thereprocase/spool-wall-rack/designs/rev-g2/ef-triangulated-v1/README.md

# E + F direct-brace body

Implemented CAD: a six-millimetre-wide diagonal connects the lower mounting region directly to the keel. The upper mast retains the six-millimetre web and tapered shoulders from ef-cut-v4. Protected G bearing/capture geometry has zero symmetric difference; fixed mounting and moulding checks pass.

The original two-wall, 0.6 mm skin schedule in selected-layout.json was not sliced. Subsequent implemented ASA schedules retain this body and use 1.6 mm skins. They provide aligned body/helper STEP files, model-only 3MF, actual slices and verification.

https://github.com/thereprocase/spool-wall-rack/tree/main/designs/rev-g2/print-controls

CAD validity does not establish structural performance or physical print qualification. Sacrificial bridges receive zero structural or bond credit.

Combined STEP

https://raw.githubusercontent.com/thereprocase/spool-wall-rack/main/designs/rev-g2/ef-triangulated-v1/bracket-with-modifiers.step

Body and individual aligned helper STEPs

https://github.com/thereprocase/spool-wall-rack/tree/main/designs/rev-g2/ef-triangulated-v1
