thereprocase/spool-wall-rack/designs/rev-g2/evolution/f9ad9cdbc331/README.md

# G helper candidate f9ad9cdbc331

Selection role: **balanced**. Experimental CAD, not a qualified bracket or load rating.

[Combined body/helper STEP](bracket-with-modifiers.step) · [Model-only 3MF](rev-g-model-and-modifiers.3mf) · [Body STEP](body-only.step) · [Actual Orca slice and settings](slice-evidence.zip)

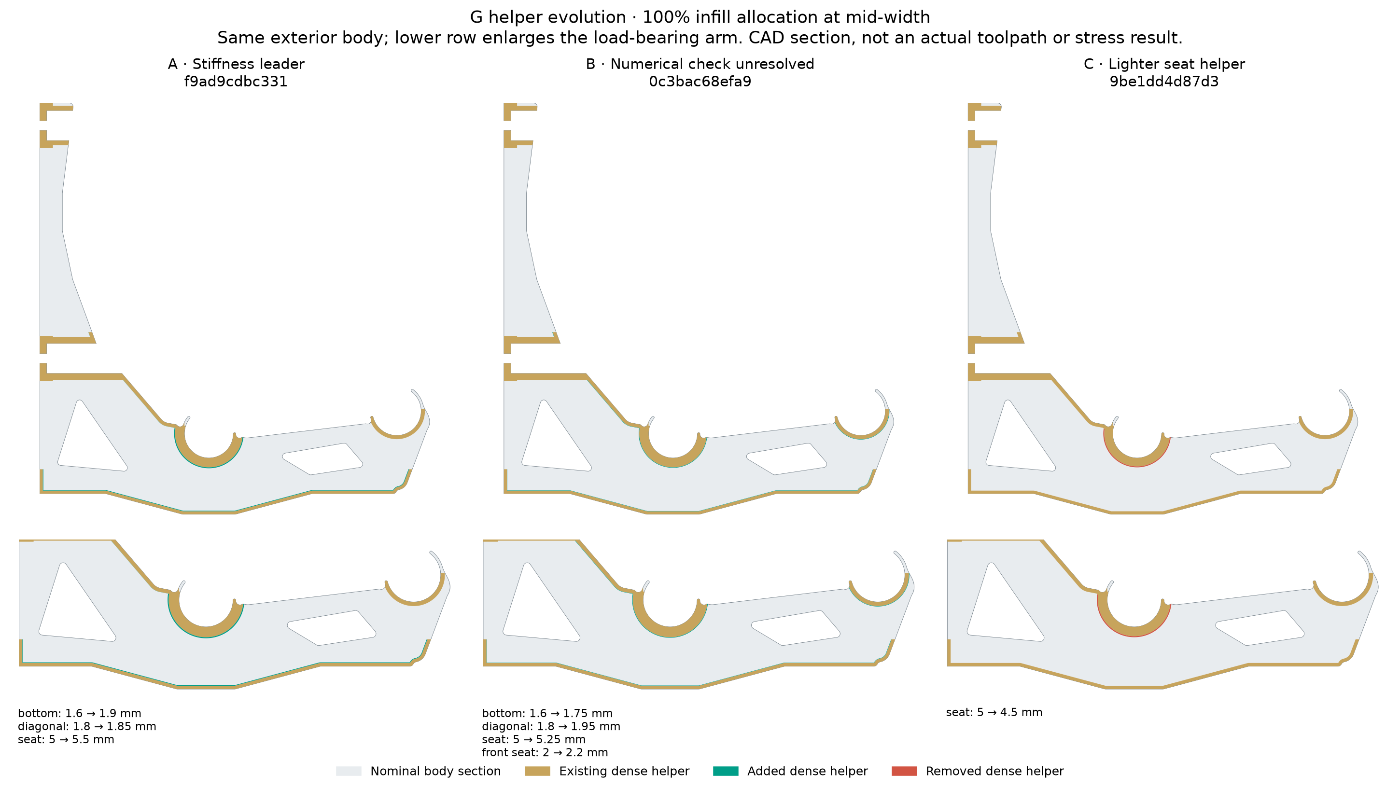
[picture p52: analysis/rev-g2/evolution-results/batch-02/helper-directions.png]
Helper allocation comparison


The exterior body is byte-identical to G. These dimensions change the aligned 100% infill helper allocation:

| Parameter | mm |
|---|---:|
| bottom band | 1.9 |
| diagonal band | 1.85 |
| seat band | 5.5 |
| front seat band | 2 |
| lower tunnel collar mm | 3.5 |
| upper tunnel collar mm | 2.5 |

Import the model-only 3MF as one object with multiple parts. The body prints; the three helpers are 100% rectilinear infill modifiers. External tabs and halos must stay modifiers. Use OrcaSlicer, P1S/0.4 mm, calibrated PETG settings, at least two walls, five 0.2 mm top/bottom layers and 0% base infill. STEP carries geometry and alignment, not slicer roles.

Individual helpers: [dense chords and seats](dense-chords-and-seats.step), [lower internal plane](rib-plane-lower.step), [upper internal plane](rib-plane-upper.step). [CAD checks](helper-verification.json), [body provenance](source-verification.json), [3MF role checks](3mf-verification.json), [hashes](SHA256SUMS.json).

At 12 kg, the retained-material screen gives **4.1295 mm** maximum movement and **20.4292 MPa** raw tensile stress. Contact and equilibrium pass at the stated 1e-5 screen tolerance. The model omits 8.12% of nominal raw plastic.

The completed full-cell refinement on the same retained material gives
**4.1547 mm** maximum movement and **19.6792 MPa** raw tensile peak. The maximum
change across all 10,234,400 compared nodes is 0.025293 mm. All 67,740,528
stress samples are retained. Active preparation, solve, audit and comparison
take 5 min 18 s. This checks adaptive coarsening error; boundary omission and
physical qualification remain unresolved. Small raw-stress differences are
not a demonstrated strength ranking.

[Full-cell audit](../../../../analysis/rev-g2/evolution-results/batch-02/leader-refinement/audit.json) ·
[Mesh comparison](../../../../analysis/rev-g2/evolution-results/batch-02/leader-refinement/mesh-comparison.json).

[Detailed 3D audit](../../../../analysis/rev-g2/evolution-results/batch-02/f9ad9cdbc331/audit/audit.json) · [Search workflow and qualification limits](../../../../analysis/rev-g2/EVOLUTION.md).

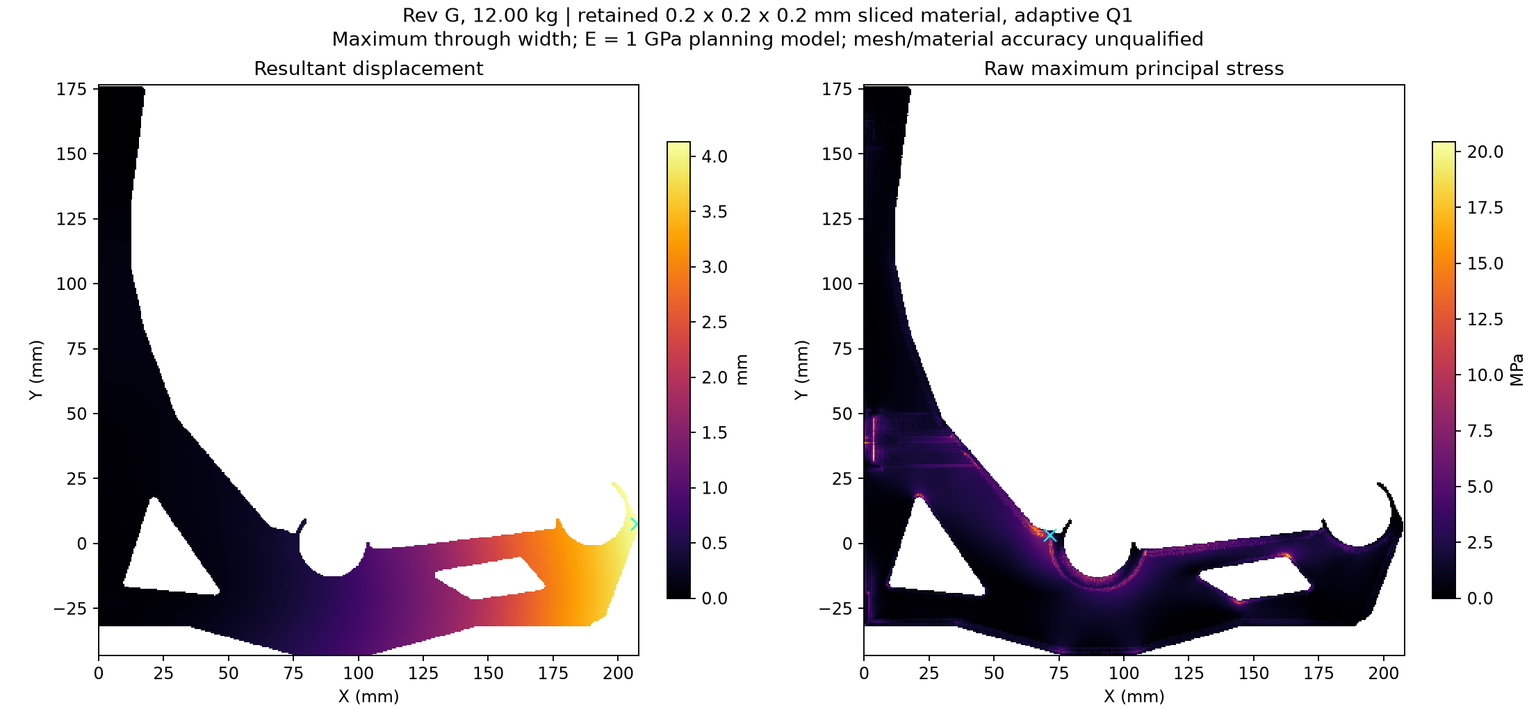
[picture p53: analysis/rev-g2/evolution-results/batch-02/f9ad9cdbc331/audit/g-results.png]
Retained-material movement and raw stress
