thereprocase/spool-wall-rack/designs/rev-g/studies/seed1-best/README.md

# Rev G seed-1 coarse best — rejected diagnostic candidate

Candidate `82e88fcf29749880c5c3` uses thin shaped planes. It slices to
**84.35 g**, but gives 4.930 mm vertical movement, 5.034 mm mean seat
translation magnitude and 120.46 MPa raw maximum tensile stress in the h2
3D model. Its fine 2D movement of 4.001 mm already narrowly exceeds the
4 mm bracket planning screen. No acceptance is claimed.

The 3MF imports all three modifiers in alignment and keeps windows/tabs empty,
but minimum dense footprint coverage is only 94.98% at an upper-skin bridge
transition. The failed coverage gate remains recorded.

[Exact parameters](selected-layout.json) · [Actual toolpath audit](toolpath-verification.json)
· [Model-only 3MF](rev-g-model-and-modifiers.3mf)
· [Raw mechanics](../../../../analysis/rev-g/studies/seed1-best/README.md)
· [Study report](../../../../analysis/rev-g/README.md).
