thereprocase/spool-wall-rack/analysis/rev-g/studies/full-plane-best/README.md

# Full-plane feedback finalist — three-mesh evidence

The actual slice is 103.76 g. All three saved meshes pass independent
equilibrium/contact gates but fail the raw 10.125 MPa tensile screen.
The fine peak is 55.05 MPa; it is not a converged rupture allowable.

| Mesh | Complete finite field | Equilibrium results | Mesh audit |
|---|---|---|---|
| h2 | [NPZ](print-material-1w-h2-solution.npz) | [JSON](print-material-1w-h2-results.json) | [JSON](print-material-1w-h2-mesh-quality.json) |
| h1.5 | [NPZ](print-material-1w-h1.5-solution.npz) | [JSON](print-material-1w-h1.5-results.json) | [JSON](print-material-1w-h1.5-mesh-quality.json) |
| h1 | [NPZ](print-material-1w-h1-solution.npz) | [JSON](print-material-1w-h1-results.json) | [JSON](print-material-1w-h1-mesh-quality.json) |

[Geometry audit](geometry-1w.json) · [Parameters](selected-layout.json)
· [Search provenance](search-selection.json) · [Quadratic buckling](../../BUCKLING.md)
· [Actual CAD/slicing](../../../../designs/rev-g/studies/full-plane-best/README.md)
· [Raw-peak metrics and interpretation](../../README.md).
