thereprocase/spool-wall-rack/analysis/rev-g/studies/seat-support/README.md

# Wider inner-seat support — rejected 3D feedback perturbation

The 5 → 8 mm inner-seat support change reduces coarse front movement to
2.988 mm, but the raw h2 tensile peak is 21.25 MPa. The actual slice is
108.03 g. No refined strength acceptance is claimed.

[Design rationale](design-rationale.json) · [Parameters](selected-layout.json)
· [Complete h2 field](print-material-1w-h2-solution.npz)
· [Equilibrium results](print-material-1w-h2-results.json)
· [Mesh audit](print-material-1w-h2-mesh-quality.json) · [Geometry audit](geometry-1w.json)
· [Actual CAD/slicing](../../../../designs/rev-g/studies/seat-support/README.md)
· [Full study](../../README.md).
