thereprocase/spool-wall-rack/analysis/rev-g/studies/seed1-best/README.md

# Thin seed-1 candidate — retained failure evidence

The complete h2 field gives 4.930 mm vertical movement and 120.46 MPa raw
maximum tensile principal stress. Movement, strength and actual dense-path
coverage fail. No finite stress cells are removed.

[Raw solution](print-material-1w-h2-solution.npz) · [Equilibrium results](print-material-1w-h2-results.json)
· [Mesh audit](print-material-1w-h2-mesh-quality.json) · [Geometry audit](geometry-1w.json)
· [Parameters](selected-layout.json) · [Search selection](search-selection.json)
· [Actual CAD/slicing](../../../../designs/rev-g/studies/seed1-best/README.md)
· [Full study](../../README.md).
