thereprocase/spool-wall-rack/RESTART-2026-09-11.md

# Current restart: recovered E13 ASA reference and rejected EF core trial

Read designs/rev-g2/print-controls/README.md and RECOVERED-PRINTS.md first. A read-only recovery found the completed overnight ASA slice associated with E13: seven walls, 10% base infill, 1.6 mm minimum skins and two objects. Its associated downloaded STEP is byte-identical to the published E13 assembly. The newer STEP is G. The saved G PETG project uses two walls and 10% base infill with all three helpers, but was saved after print start. The exact original PETG submission was overwritten; current archive/cache use a later PLA profile. Do not call the deliberate eight-wall G control a recovered successful physical print.

Current EF direct-brace body and continuous core are built and sliced, with aligned helper STEPs, complete source hashes and raw bond audits. Four walls / 1.6 mm skins in ASA use 91.970652 cm3, versus deliberate G eight-wall control 118.660028 cm3. Gross cut 27.048%, core reinvestment 5.406 cm3, net saving 22.492%. Local credited routes pass, but the part fails the movement allocation.

Intermediate 1e-4 contact diagnostics: thick G 2.672976 mm, raw tensile peak 21.000368 MPa; EF core 4.981787 mm, raw peak 32.195513 MPa. Omitted raw nominal material is 4.734% and 8.902% respectively. Both tighter 1e-5 attempts fail their time bounds. Preserve every field and raw failure. Do not label either a tight accepted result or a physical rating. Core refinement and a winning broad architecture remain unfinished.

Raw controls are under analysis/rev-g2/.work/print-controls. G's accepted intermediate is g-asa-8w-1p6/finish-02/discovery; core is ef-core-asa-4w-1p6/finish-01/discovery. Each has failed tighter solve evidence and a separate intermediate audit. Original printer recovery data, identifying job records and source archives remain only in ignored analysis/rev-g2/.work/print-recovery. Do not publish those raw archives. The public receipt is designs/rev-g2/print-controls/recovered-print-evidence.json.

Next: use the recovered successful E13 schedule as the physical-reference lead, preserving its geometry association limits; use deliberate G controls to isolate architecture and wall count. Restore or capture the actual submitted PETG slice before calling it matched. Reassess direct frame bending and the forearm using the current fields; do not keep adding core material after the stiffness failure. The broad fast-ranking method and material-converged qualification remain unfinished. Existing GPU fixtures, previous G pilot, failed EF diagnostics and all old CPU caches stay preserved. No stopped whole-part CPU meshing was restarted.

## Prior checkpoint history

# Restart handoff: implemented EF cut and localized reinforcement

**Latest implemented work:** `analysis/rev-g2/EF-RESULTS.md`. The selected E+F
body is now built and sliced. Protected G seat geometry has zero CAD XOR;
mounting axes and 25.4 mm horizontal moulding underside pass their checks.
Five implemented schedules have complete aligned STEP/helper handoffs.

`ef-cut-v3` cuts 29.211% of matched G spent extrusion. `ef-reinvest-v1` adds
6.342 cm3 at inner-seat/forearm, wall/upper-brace and seat/keel-post transitions,
leaving 20.653% net saving. Mechanics are underway; do not promote either as a
load-qualified winner. If local reinforcement needs more budget, cut from
low-stress/low-strain-energy regions while rechecking all load cases,
connectivity, stability and print support. Track gross cut, added back and net
saving separately. No need to ask again about the moulding datum.

The heavier first EF reference has an accepted 1e-5 contact screen:
5.660824 mm movement and 39.997226 MPa raw tensile peak, worse than G. The
successful solve first settles contact at 1e-4, then verifies it at 1e-5.
The final check takes 59.75 s including all stress export, after 271.81 s
contact discovery. Earlier strict-from-start and stronger-coarse failures
are retained. This timing excludes initial failures and geometry/CAD setup.
Current cut/reinforced pipeline attempts live under each candidate's
`analysis/rev-g2/.work/<candidate>/check-01`. Public receipts are under
`analysis/rev-g2/ef-hybrid-results/`. No old CPU whole-part meshing was restarted.

**Earlier continuation context:** [six broader body sketches](designs/rev-g2/shape-seeds/README.md)
and [fixed interface contract](designs/rev-g2/INTERFACE-CONTRACT.md). The body
must no longer be copied unchanged from G. Change outer contours, depth, braces,
windows and through-width material arrangement. Keep rods at `(90,0)` and
`(190,12)` in XY and mounting axes at `(164,12)` and `(40,12)` in YZ, plus spool
clearance. The locating datum is now resolved: printed G brackets slide down
the wall until their bottom edge rests on the crown moulding. Preserve the
lower wall corner at X=0, Y=-32 mm and the rod/mount heights relative to it.
Keep the underside horizontal for at least 25.4 mm outward from the wall
before descending. Actual moulding projects 19.05 mm. This replaces the
15 mm estimate; do not use the old 215 mm limit or local E13-minus-8-mm floor.
The selected next body is E plus F: deeper E frame with F-derived seat backing.
The six new seeds are connected XY sketches with a spool-clearance check,
not CAD/STEP handoffs or a mechanically ranked family set.

The local G pilot is completed and preserved. Two of its three actual-slice
finalists converge; the other fails both its initial solve and bounded retry.
The leader's same-material uniform 0.2 mm refinement completes in 318.10 active
seconds, giving 4.154745 mm maximum movement, 19.679217 MPa raw tensile peak,
and 0.025293 mm maximum change across all 10,234,400 compared nodes. All
67,740,528 stress samples survive. See the loop's calibration and leader-refinement
receipts. It still exceeds the 4 mm allocation, retains 8.12% material omission,
and does not establish strength or transfer accuracy for new architectures.

**Completed local method pilot:** [staged evolutionary screening](analysis/rev-g2/EVOLUTION.md).
The local G helper screen now evaluates 100 new proposals in 11 min 18 s.
The first real CAD/slice/3D finalist pass took 6 min 55 s. Use the loop page
and its receipts for finalist and refinement status. This screening workflow
supersedes the earlier requirement to finish all material qualification before
running local allocation experiments. Qualification gates remain intact.

New scripts are `evo_screen.py`, `evo_search.py`, `evo_verify.py`,
`evo_refine.py`, `evo_transfer.py`, `evo_uniform.py` and `evo_report.py` under
`analysis/rev-g2`. `evo_refine.py --prepare-only` permits CAD/material preparation
while another candidate uses the GPU; `--resume` runs its solve and audit.
Reported active-stage time excludes time parked between those invocations.
Keep GPU solves sequential on the 12 GiB device.

The actual P1S material parser now restores the configured nozzle offset.
Preserve the superseded P1S caches. Historical G mechanics uses a zero-offset
slice and is unchanged. Fresh corrected P1S evidence and all candidate fields
live under `analysis/rev-g2/.work/evolution`; no raw evidence is deleted.

Fresh 10.75 / 12 / 13.25 kg G contact checks are documented in [G results](analysis/rev-g2/G-RESULTS.md). One spool changes bracket movement by about 0.452 mm; material accuracy and physical qualification remain open.

This is the current restart checkpoint. The long whole-part CPU meshing route
has been stopped. Preserve the current working tree, including untracked raw
attempts and ignored runtime caches. Do not restart the old fTetWild jobs.

**Current continuation:** [G results, numerical sensitivity and limits](analysis/rev-g2/G-RESULTS.md).
The retained 0.2 mm material now has a completed unilateral wall-contact screen:
4.335477 mm maximum movement and 20.025374 MPa raw peak tensile stress at 12 kg.
A 1e-6 relative solve check keeps the 6,426-node contact footprint and changes
all nodal displacements by at most 4.894e-7 mm versus the 1e-5 screen.
This does not pass the original stricter solver gate or establish material
accuracy: 8.0177% of raw nominal material is omitted. See the result page for
fresh spool-load checks, preserved failures and final checkpoint receipts.

**Resume from the completed contact state**, not from the original bilateral
wall restraint. The coarse correction and changed-load contact fixtures pass.
The next principal uncertainty is finer material/mesh convergence on G and
transfer to the fresh P1S/PETG slice. Keep all raw stress fields, earlier failed
iterates and geometry caches. No old CPU meshing job should be restarted.

**Previous continuation:** [adaptive mesh and full-G trial evidence](analysis/rev-g2/ADAPTIVE-MESH.md).
Two-level constrained hex coarsening and its CUDA operator pass independent
mechanical fixtures. Protecting G's interfaces and split-bond neighborhoods
reduces 8,265,873 fine cells to 4,096,575 leaves. Both full-G GPU trials failed
linear convergence; all fields and peaks survive. A separate geometry census
reaches 0.025 mm XY boundary cells with 1.10% omitted raw material, before
grading/constraints/mechanical refinement. A fresh P1S/PETG slice and raw shape
were built after accounting separately for startup priming extrusion. They
have not replaced the historical shape in a converged mechanics loop.

**Previous continuation:** [GPU validation and reproduction](analysis/rev-g2/GPU-VALIDATION.md).
Warp 1.17.0 is installed and tested on the RTX 3080 Ti. The upstream elasticity
comparison, independent 3D hollow-material/contact fixtures and manufactured
patch tests on G's actual raw slice crop pass. Conservative voxel geometry
still removes 4.31% of that crop at 0.1 mm XY / 0.2 mm Z spacing. This is not
an accepted whole-G material mapping, load solution or strength result.

## Current candidates and decisions

[STEP/helper download index](PRINT-CANDIDATES.md) lists all implemented recent ideas and the five current G recheck schedules. Every future idea checkpoint must include aligned body/helper STEP files and notes. G2 concept-family CAD and helper exports are required unfinished work after restart.

- [Rev G research finalist and CAD](designs/rev-g/README.md): latest implemented
  research geometry. It is not a qualified design. Its original structural
  approximation is superseded for interpreting actual printed material.
- [E13 handoff](designs/closed-wall-e13/README.md): preserved earlier prototype evidence;
  it does not acquire new qualification from G2 work.
- [G2 architecture worksheet](designs/rev-g2/ARCHITECTURE-WORKSHEET.md): seven
  preparatory families, not seven completed CAD candidates. No G2 architecture
  has been built, ranked, or accepted.
- [G2 requirements](G2-BRIEF.md) and the current interface contract govern the
  new study. Existing outlines and helper count/shape are soft; reference rod
  and mounting positions now stay fixed. The matching moulding locating datum
  and one-inch horizontal reach replace assumed old silhouette constraints.
- [GPU execution checkpoint](analysis/rev-g2/GPU-VALIDATION.md) follows the
  [software review](analysis/rev-g2/GPU-FEM-REVIEW.md). Warp's Apache-2.0 license,
  tagged example hash and wheel/JIT CUDA execution are verified. DTU reuse
  permission was not established and its code was not incorporated. The tested
  GPU backend is a starting point; its current full-cell material approximation
  and diagonal preconditioner are not qualified for a whole-G solve.

## Preserved requirements

P1S, 0.4 mm nozzle, PETG or ASA, at least two walls, 0% base infill and 100%
helper regions. Sacrificial 0.4 mm bridge extrusion counts toward spent plastic
but receives zero stiffness, strength or bonded-connection credit. Keep all
finite stress cells and raw peaks. No percentile substitution.

Reference load is 12 kg / 117.72 N per bracket. Total loaded movement limit is
5 mm; the provisional rail/mount reserve is 1 mm, leaving 4 mm for bracket
resultant movement. Adding/removing a 1.25 kg spool requires a new contact solve
and at most 1 mm total movement change. The effective 1 GPa modulus is a
planning assumption, not measured lifetime behavior. Sustained 85 F and brief
loaded 100 F exposure, nominal fracture factor four, rail sag, mount slip,
creep, fit and print-process qualification remain explicit gates.

## Completed sliced-material work

[Analysis overview and reproduction](analysis/rev-g2/README.md) links the raw
slice archives, independent validation, process audit and reference shape cache.
Five schedules were actually sliced: 2w/2 skins, 2w/5 skins, 2w/8 skins,
8w/2 skins and 8w/8 skins; each skin layer is 0.2 mm. G's body and three original
helpers were copied without geometry changes. All five effective process
settings and P1S bed/exclusion checks passed.

The independent 50,000-sample shape check passed outside the stated 0.005 mm
polygonization uncertainty. It uses analytical distances to variable-width
paths rather than querying the same polygon union twice. Thick bridges are
excluded before connectivity and geometry queries.

| Schedule | Credited E volume, mm3 | Sacrificial E volume, mm3 | Nominal structural union, mm3 |
|---|---:|---:|---:|
| 2w / 2 skins | 60373.785 | 6901.280 | 61393.747 |
| 2w / 5 skins | 70979.802 | 6940.469 | 71890.970 |
| 2w / 8 skins | 81247.882 | 6928.297 | 82057.762 |
| 8w / 2 skins | 103417.432 | 5060.135 | 104686.248 |
| 8w / 8 skins | 119735.998 | 5089.798 | 120769.740 |

Nominal footprint volume is a separate continuum quantity from extrusion E.
Do not erase the difference or call them equal. The reference cache loads in
about 1.6 s; 10,000 occupancy queries took about 0.06 s on this machine.

`PlasticShape.integrated_volume(regions)` integrates exact polygon intersections
through all layers. Independent analytic slab fixtures pass for raw/continuum,
empty, disjoint and overlapping queries, with one/four workers. The whole
reference projection agrees with nominal volume within about 2.1e-8 mm3.

## Latest completed mechanical diagnostic

The final reduced reference uses exact material-volume integration per P1
triangle. All finite triangles are retained, and no stiffness is inserted at
empty quadrature samples. The two runs are:

| Mesh | Triangles | Front mean vertical movement, mm | Global maximum resultant, mm | Raw tensile peak, MPa |
|---|---:|---:|---:|---:|
| h2 | 37985 | 3.097760 | 3.462327 | 13.230930 |
| h1 | 70035 | 3.111314 | 3.477636 | 11.741875 |

Front movement changes about 0.44%. Both retain nonzero wall gaps and pass free
residual, force, moment, nonpenetration and active-reaction checks. The full
finite displacement, stress, material-volume, force and reaction fields are in
[reduced-plastic](analysis/rev-g2/reduced-plastic). Use only the filenames with
`-exact-h1` or `-exact-h2` for the current reference.

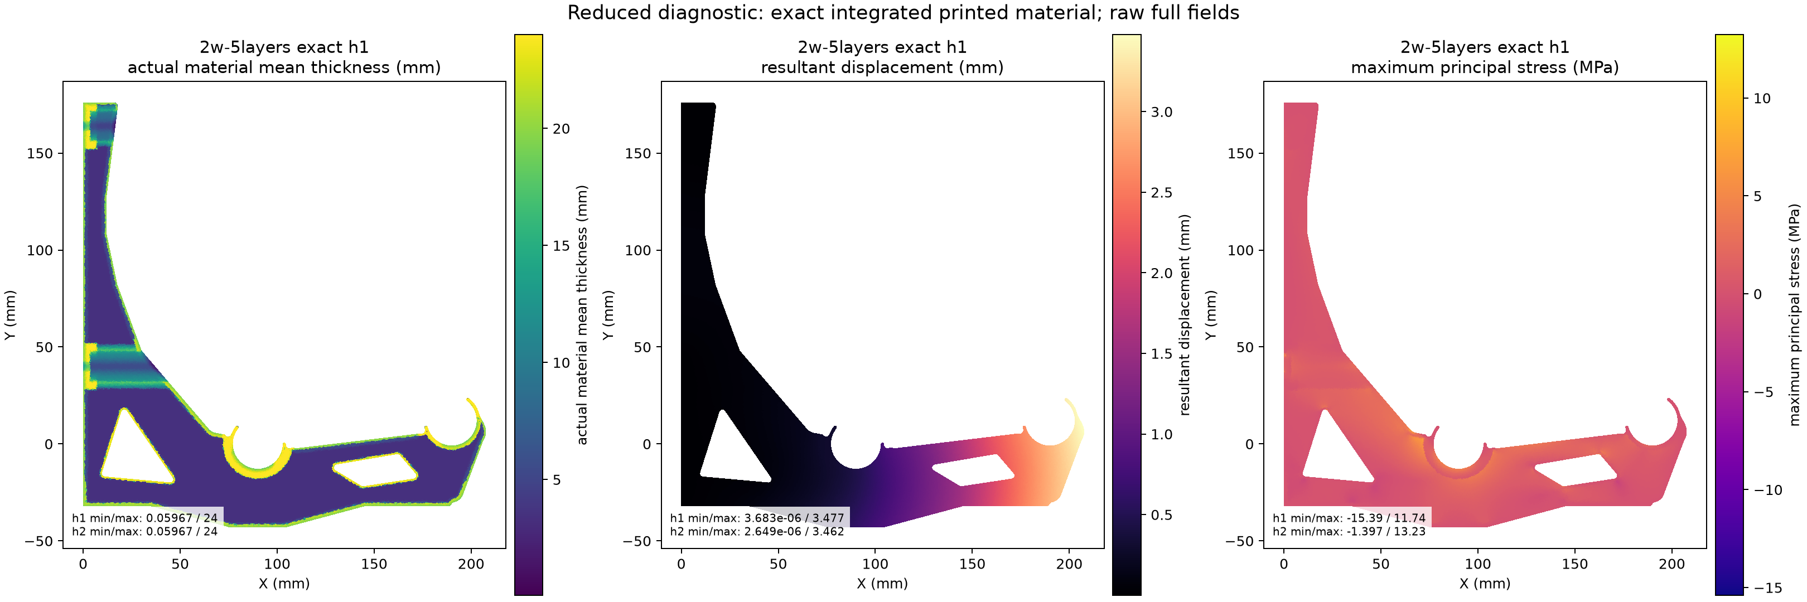
[picture p55: analysis/rev-g2/reduced-plastic/exact-recheck.png]
Latest reduced diagnostic


This is plane stress with displacement uniform through bracket width and
fixings projected to the wall boundary. It collapses the actual 3.6 mm washer
plane and through-width response. It is not a 3D strength result. Raw peak
stress is not converged. No corrected 4x fracture margin is established.

The attempted extension to the other schedules is unfinished: 2w/2 skins hit
the positive integrated-element-volume assertion, and 2w/8 skins exited during
integration without a result. Neither eight-wall reduced run was completed.
Investigate these failures before claiming a complete reduced matrix. Earlier
quadrature-based beta outputs remain local historical attempts and are not the
accepted diagnostic.

The actual production contact kernel passes analytic opening, closing,
touching and release fixtures. Affine elasticity/stress and rigid motions also
pass. [Fixture report](analysis/rev-g2/validation/mechanics-fixtures.json).

## 3D failures and why the route changed

[Meshing notes](analysis/rev-g2/MESHING-NOTES.md) retain the attempt history.
The reference continuum uses 0.03 mm closing, pore areas below 0.16 mm2,
0.02 mm XY simplification and a 0.01 mm coordinate grid. Its volume is
71949.034 mm3, with a 206.314 mm3 symmetric difference from raw footprints.
Raw nominal layers remain separately preserved.

TetGen recovered the boundary and 39 enclosed voids, but quality refinement
failed. Its boundary-only mesh has 662332 retained tetrahedra after auditing
268 numerically collapsed cells. The cleanup introduces 67 nonmanifold boundary
edges and artificial internal faces as far as 0.4 mm from the intended surface.
It is rejected despite nearly exact total volume. Netgen optimization crashed;
rounding and T-junction repair did not produce an accepted quality mesh.

Both fTetWild G jobs remained CPU-active for over an hour without returning a
mesh. They were explicitly terminated and process absence verified. No G 3D
solve was accepted. Small hollow-box meshing/refinement fixtures do not prove
the bracket is solved.

## Local evidence and tools to preserve

The active branch is `codex/rev-g2-architecture`; the public delivery branch is
`main`. This checkout was created independently of the earlier Rev G worktree.
Do not reset/clean either worktree, delete raw attempts, or modify E13/G records.

Current scripts and outputs are under `analysis/rev-g2` and `designs/rev-g2`.
The established native worker is `analysis/rev-g/run_native.py`; the Python
environment and installed Orca application are outside the repository. Base
dependencies are in `analysis/e13/requirements.txt`, with additional isolated
packages listed in `analysis/rev-g2/requirements-extra.txt`.

The new GPU runtime is separate from that native CAD environment. Its pinned
dependencies are in `analysis/rev-g2/requirements-gpu.txt`; instructions are in
the GPU checkpoint. `gpu_benchmark.py`, `gpu_hex.py`, `validate_gpu_hex.py` and
`gpu_material_probe.py` reproduce the new backend, numerical fixtures and slice
crop tests. Accepted and rejected numerical fields are in
`analysis/rev-g2/gpu-validation`, including its `failures` and `refinement`
directories. The latter contains the complete finer crop fields, not a G solve.

Keep these local runtime/evidence locations, even when they are not published:

- `analysis/rev-g2/.work/python`: isolated native meshing dependencies.
- `analysis/rev-g2/.work/integrated-thickness`: exact-integration caches.
- `analysis/rev-g2/.work/*gpu*research.md`: supplementary software research.
- `analysis/rev-g2/.work/gpu-route`: runtime discovery snapshots and raw GPU
  logs, including initial failed comparisons and the fixture count correction.
- `analysis/rev-g2/g-recheck/2w-5layers/fallback-investigation`: raw failed
  repair/refinement experiments and their reports. Some exploratory scripts
  still need review before redistribution or reuse.
- Other local continuum/decimation attempts, original uncompressed layer JSON,
  duplicate G CAD copies and untracked native debug STL files. They are not new
  accepted designs. The published slice ZIPs preserve the canonical raw inputs.

No analysis worker from the latest G jobs needs to survive the restart. Do not
terminate unrelated historical processes merely because their names are Python.

## Resume sequence

1. Read this handoff, `AGENTS.md`, `G2-BRIEF.md`, the analysis README and GPU
   review. Verify the current git state; preserve uncommitted work.
2. Continue from the tested Warp backend. Upstream default-tolerance stress
   comparisons failed; the explicitly tighter default-case comparison passes
   the original gate. Independent affine/rigid, hollow-wall, 3D bar contact,
   edge/corner bond and sacrificial-connector fixtures pass. Preserve all raw
   results; these checks do not establish whole-bracket mechanics.
3. Resolve the measured voxel boundary loss and full-part bond representation
   with a bounded adaptive/cut-cell or sufficiently converged full-cell study.
   The current crop loses 17.12%, 8.37% and 4.31% at successively finer XY grids.
   Check long thin bending and practical preconditioning before full-G scale;
   the earlier diagonal-only solver has now been supplemented by the tested
   auxiliary coarse correction in `gpu_multigrid.py`. Avoid returning to
   unbounded whole-part tetrahedral meshing.
   Continue from `gpu_demo_adaptive.py` and `gpu_demo_adaptive_operator.py`:
   two-level constraints now pass, and `gpu_demo_boundary.py` quantifies finer
   full-G material recovery. Extend grading/constraints to that boundary mesh
   using the completed contact state and the tested coarse correction. The
   existing diagonal-preconditioned full-G trials failed even after 12,000
   continuation iterations. Fresh P1S/PETG priming accounting is repaired;
   preserve its distinct raw shape and the original accounting failure.
4. Adapt and verify the actual seat loads, washer plane, bore restraints and
   nonzero-gap wall interfaces. Recheck G with corrected 3D material and mesh
   sensitivity, then the changed spool load. Repair the unfinished reduced
   matrix application as needed.
5. Only then build and compare the six-or-more G2 architecture families, obtain
   early 3D feedback, optimize survivors, and publish the complete candidate
   ledger. No preferred prototype until all computational gates pass.

Physical qualification and measured dowel dimensions remain outstanding. A
simulation result alone must never become a released spool rating.
