thereprocase/spool-wall-rack/docs/archive/AGENTS-2026-09-11.md

# Project instructions

Keep this repository current as the design progresses. Checkpoint completed geometry and its verification with clear commit messages. Keep the current prototype obvious in README; preserve superseded useful revisions separately.

Do not commit personal information, private conversation transcripts, credentials, local absolute workspace paths, or identifying account data in project content. Use a generic project identity for git commits.

Current path is the closed-wall, continuous-plate bracket. Keep the future open-web exploration separate. Preserve full L-shaped internal plates parallel to printer XY and installed bending plane. Do not replace them with transverse grids.

Print assumptions: 0.2 mm layers; 1.2 mm top and bottom; 15% infill gets zero structural credit. E6 uses 2.4 mm modeled structural perimeter, superseding the original three-perimeter assumption locally; verify actual sliced paths. Internal and exterior side plates remain 1.2 mm. Snap fingers are separately dimensioned.

Do not assign safe spool counts from generic tensile strengths. State limits of geometric checks and distinguish geometry, slicing, mechanical analysis and physical validation. Never label prototype G-code or a geometry-only 3MF as a validated print profile.

Update the README design journal at meaningful checkpoints. Include actual CAD screenshots or drawings, the reason for each change, validation outcomes and the concrete next step. Keep the newest prototype and image prominent so a reader can follow progress by refreshing GitHub. Do not substitute a plan for completing authorized work.

Snap roots must transition smoothly into the bearing seat. Do not use intersecting circles over a stepped profile as a substitute for tangent root blends. Round relief-slot ends and inspect the actual integrated bracket profile, not just an isolated retainer. Current reference is E8.

When replacing a feature, remove its obsolete precursor geometry. Do not leave redundant lips, support nodes or prongs behind a new retainer. Inspect the full integrated outline at both seats.

E6 final geometry requires finish_cad.py after profile export. Preserve matching cavity-rim reinforcement behind the mirrored 3 mm broad-face chamfers. Smoothly taper large edge treatments to zero before small features; do not apply their nominal radii to thin snap noses.

E6 uses 100 mm rail spacing, 90/190 mm rail centers, a full wall plane from -32 to +176 mm, and screw centers at 164/12 mm. E5 is a rejected fixed-span thinning study. Preserve the stated handling-stability tradeoff; the I/L^3 comparison is a screening proxy, not whole-bracket stiffness or a load rating.

Service envelope: 85°F sustained; 100°F for six hours/year, fully loaded. Work PLA, PETG, ASA and PA6-GF cases. E6 material report selects ASA for the first prototype, not a released rating. The 12 kg sustained/hot and 24 kg brief proof cases are qualification targets. Preserve PA6-GF annealed dry and water-conditioned cases separately; published typical properties and short tests do not establish years of creep life.

E7 adds 10 × 10 mm maximum cavity boxes with 1.2 mm manufacturing dividers and R2 full-cell corners, preserving four continuous 1.2 mm plates. Dividers receive no assigned structural credit. Current fixings are Y=164/40 mm; clamping lands are 3.6 mm from the wall, with Ø5.2 mm screw clearance and Ø16 mm nominal driver access. Preserve the sloping access roofs. #8/#10 and M5 shank clearance are intended; confirm printed M5 fit with the coupon. E7 STEP is distributed as bracket-step.zip; do not publish the ignored 46 MB intermediate uncompressed file. Keep the three-step build chain: SCAD profiles, finish_cad.py, verification/rendering. E7 changes the connection and does not inherit a validated E6 load rating. The 34 mm arm-depth study remains unimplemented.

Current E8 delivery supersedes the E7 grid: one solid STEP body plus two separate 1.2 mm helper slabs at print Z=7.6–8.8 and 15.2–16.4 mm. User chooses body wall count and infill and converts helpers to 100% infill modifiers. Do not model infill cells or large internal void bands, fuse the helpers into the body, or imply STEP encodes slicer settings. Keep body/helper positions aligned. Wall thickness is now slicer-controlled, not a 2.4 mm CAD shell. Preserve E7 fastener geometry. No extra helper systems or slicer project are required unless requested.

Current E8 engineering serviceability criteria: 5 mm total movement under full load, including creep/dowel/mount movement, and 1 mm change on adding/removing a full spool. Initial 1.2–1.7 mm elastic movement is acceptable, not a failure criterion. FEM is an isotropic printed-material surrogate with zero sparse-infill credit; raw stress peaks are not converged rupture allowables. Keep grade-specific lifetime/creep qualification explicit. The +12 mm raised-front idea is a separate statics study: it shifts load rearward but collides with 220 mm spools against the existing back arm. Do not treat that variant as printable or inherit level-rail FEM results. Cosmetic camber is separate from the structural rail-height change.

Current running prototype is E9: front center (190,12), rear (90,0), 2 mm mirrored broad-face chamfers with smooth runouts, nominal R2 exposed wall-facet joins. Back arm reshaped for 180–220 mm spools; current nominal clearance minimum 3.93 mm. Front buttress anchors at original Y=-24 to avoid a bottom stub. Keep 3.6 mm screw lands and two 1.2 mm helper modifiers. E8 remains the level-rail baseline, not the current downloadable design. Re-run E9 analysis rather than inheriting E8 geometry coefficients.

E9 refined screening coefficients at 12 kg are K=3466.36 MPa·mm for 8 walls and K=3159.80 for 10. Use the current guide for material scaling; these are not lifetime ratings. Mesh generation audits numerically zero-volume cells, and solver/report require an independently recomputed free residual below 1e-6. Reject failed fields even if the iterative solver reports convergence. Do not remove finite material merely to improve stress results.

Current finish revision is E10. Apply the rounded side-profile fillets first, then continuous 2 mm face chamfers. Only the skinny dowel-retainer regions get runouts; structural edge endpoints and corner blends must retain full chamfer depth. E9 FEM remains a prior-finish baseline until E10 is re-solved. Retail rod fit is provisional: checked Lowe's/Madison Mill pages give 1-inch actual diameter but no numeric production/ovality tolerance. Do not invent one or confuse 0.6 mm diametral design clearance with a verified supplier tolerance. Keep measured rod min/max unknown until measurements are available.

Current prototype is E11, superseding the E10/E9 current-status notes above. It adds 38 mm of smooth underside reinforcement beneath the inner seat and R6 rigid-shoulder blends. The seat band X=77–103 must exceed both finished plain-arm reference bands X=63–67 and 113–117 in bending I and elastic section modulus; preserve the published verification margins. Keep the functional flexible fingers and relief pockets unchanged. Both broad-face chamfers have 2 mm face inset and 50 degrees above the bed (2.384 mm rise), with smooth runouts only at thin retainers. The body print envelope is about 207.51 by 246.00 by 24 mm.

E11 has new matched E10/E11 reduced models, 8/10-wall 3D refinement and a 500 N landing refinement. Current front movement coefficients at 12 kg are K=2306.334 MPa mm (8 walls) and 2098.156 (10 walls). Do not inherit E9 values. Keep independent residual/force/moment gates below 1e-6 and retain the raw peak and mesh-topology audits. Same-domain face cleanup and remeshing are recorded; finite cells must not be deleted for their stress values. The neutral OrcaSlicer audits are local geometry checks, not delivered calibrated profiles. Their height ranges require an explicit layer_height=0.2; STEP helpers remain the user-facing modifier handoff.

Current prototype is E12. The explicit slimmer-shape request supersedes E11 adjacent-section superiority targets: added underside depth is 9.5 mm preferred and must never exceed 38/3 mm. Preserve the broader smooth blend, R6 rigid shoulders, fingers, plates, hardware and mirrored 50-degree chamfers. Do not weaken adjacent arms or add holes merely to improve a section ratio. E12 has new matched comparisons, 8/10-wall global 3D and landing refinement; coefficients are K=2472.537 and 2241.876 MPa mm at 12 kg. Accepted global meshes use same-domain cleanup and h3/h2 for 8 walls, h2.5/h2 for 10. Do not reuse the rejected h3 10-wall field. Current Arachne/Everywhere toolpath audits are local geometry checks, not calibrated print profiles. Keep the deeper E11 guide and artifacts as history.

Current prototype is E13. The requested slightly thicker angular underside uses 11 mm added depth, within the 38/3 mm cap. Preserve long straight flanks and the short flat, small corner blends, R6 rigid shoulders, fingers, plates, hardware and 50-degree mirrored chamfers. Current global mesh levels are h2/h1.5/h1 for both wall counts, with matched new h1 E12 baselines. Use refined front K=2147.972 and 1936.610 MPa mm at 12 kg. Keep raw peaks, region statistics and refinement changes visible; tiny cells alone do not establish artifacts, and no finite stress cells may be removed to improve the result. The hotspot audit and three-level results supersede earlier mesh-resolution notes. Preserve E12 and older archives.

Rev F is an explicitly requested separate stiffness/weight exploration. Keep E13's exterior outline, rod seats, fingers and mounting interfaces. Angular windows, selective ribs, shaped internal planes, local infill modifiers and projecting helper-selection tabs are authorized for Rev F, superseding the full-plane/no-void restrictions for this revision only. Compare with E13's actual sliced volume and stiffness; a reduction in CAD envelope volume is not a printed-weight result. Tabs must not print. Retain E13 as the current downloadable prototype until a Rev F handoff passes the relevant geometry, structural and toolpath checks.

Rev F's clarified objective is minimum printed mass within the existing serviceability and strength limits, with stiffness per gram reported. E13 stiffness is a comparison only. Use 5 mm total loaded movement including rails/mounts, 1 mm change per full spool, and a requested fracture factor of safety of at least four at the 12 kg reference load. Wall count, sparse infill, skin/plane thickness and local modifier geometry are optimization variables for F; the exterior outline and functional interfaces remain fixed. Retain the 1.0 GPa effective-creep-modulus planning basis and report the remaining movement budget for rails/mounts. Do not claim a demonstrated full-bracket fracture factor from reduced-model or percentile stresses; preserve all finite 3D peaks and identify any unresolved constraint honestly.

Rev F September 10 checkpoint is published as an incomplete experiment. No F candidate meets the requested 4x full-bracket fracture screen. Keep the current CAD, modifier renders and status at the top of README while preserving E13 as the established prototype handoff. The seeded evolutionary optimizer is the next sprint, documented in NEXT-SPRINT.md; do not describe it as implemented or its candidates as qualified.

Rev G is authorized to complete the queued evolutionary optimization sprint and publish when complete. Inherit Rev F serviceability/strength objectives and protected interfaces. Preserve the complete F checkpoint. Implement a seeded repeatable search, verify accelerated evaluation against the canonical solver, rank finalists by actual Orca volume and retain 3D stress/buckling failures. Report computational feasibility separately from physical qualification.

Rev G search sprint is complete with no verified feasible finalist. Preserve its 1,458-candidate ledger, exact cached replays, canonical evaluator checks, actual sliced masses, all finite 3D fields and quadratic buckling evidence. The current research download is the 103.76 g full-plane feedback finalist, not an accepted design: h1 gives 3.246 mm vertical movement and 55.05 MPa raw tensile peak. The fine peak lies beside a preserved exterior chamfer. Keep E13 as the established prototype handoff and the F checkpoint archived. The next study must address local geometry/material evidence without relaxing the 4x screen or removing finite cells.

G2 is authorized as a new broad architecture study in designs/rev-g2 and analysis/rev-g2; G2-BRIEF.md governs. Preserve E13 and G artifacts unchanged. Exterior shape, internal architecture, rail positions and fixing positions are soft, subject to re-established functional requirements and compact spool-relative elevation with up to 8 mm additional downward allowance. No frozen material regions or fixed helper count/shape. Target P1S, 0.4 mm, PETG or ASA, with at least two walls. Before architecture selection, correct G's structural material model against actual Orca slices at 0% base infill with 100% helpers. Validate many-wall/few-skin and few-wall/many-skin schedules. Count 0.4 mm bridge extrusion in plastic use but assign it zero stiffness, strength and bonded-connection credit. Re-solve the corrected material domain; do not turn an unverified shell/core approximation into a requirement for special helpers or a physical failure claim. Keep every finite stress cell and all engineering gates.
