thereprocase/spool-wall-rack/analysis/e9/fem-3d-10w.png

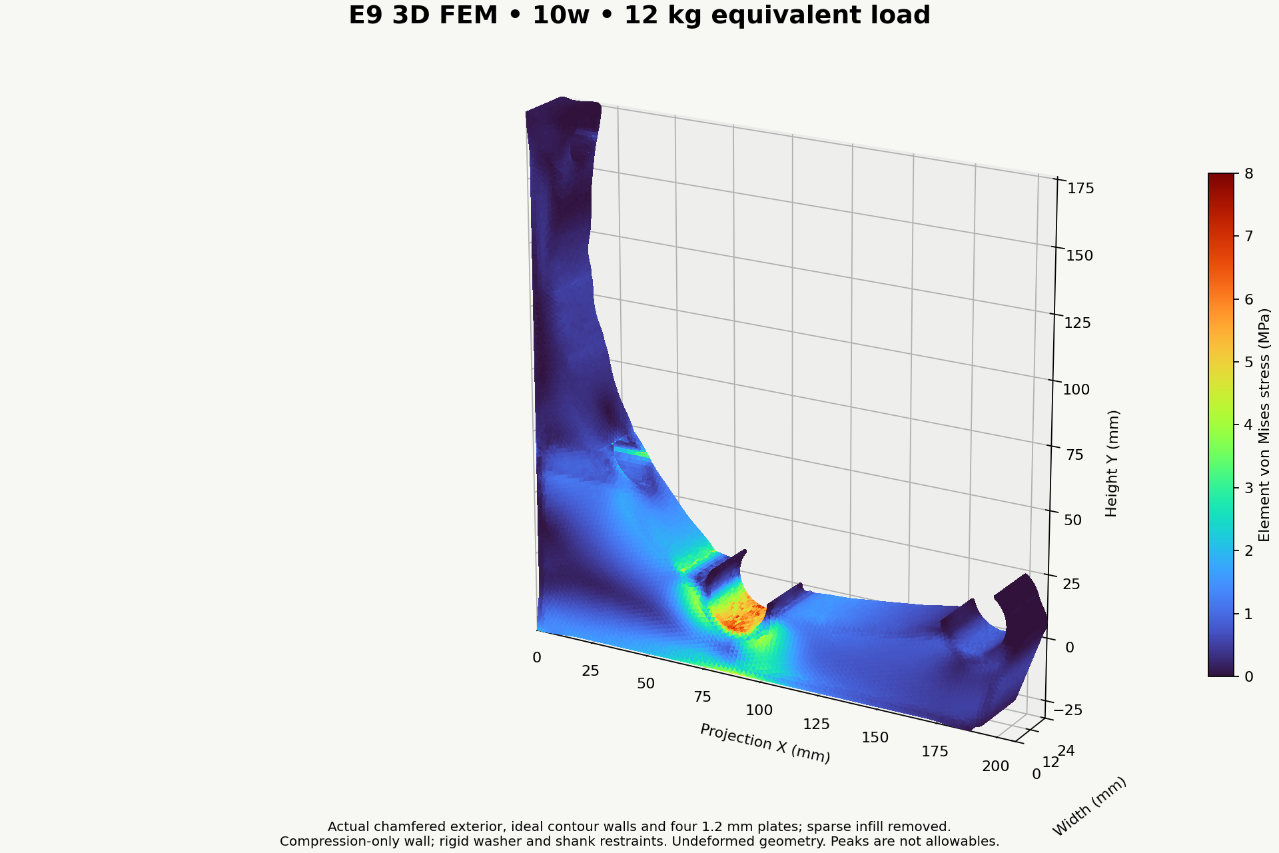
analysis/e9/fem-3d-10w.png
