thereprocase/spool-wall-rack/analysis/e11/fem-3d-10w.png

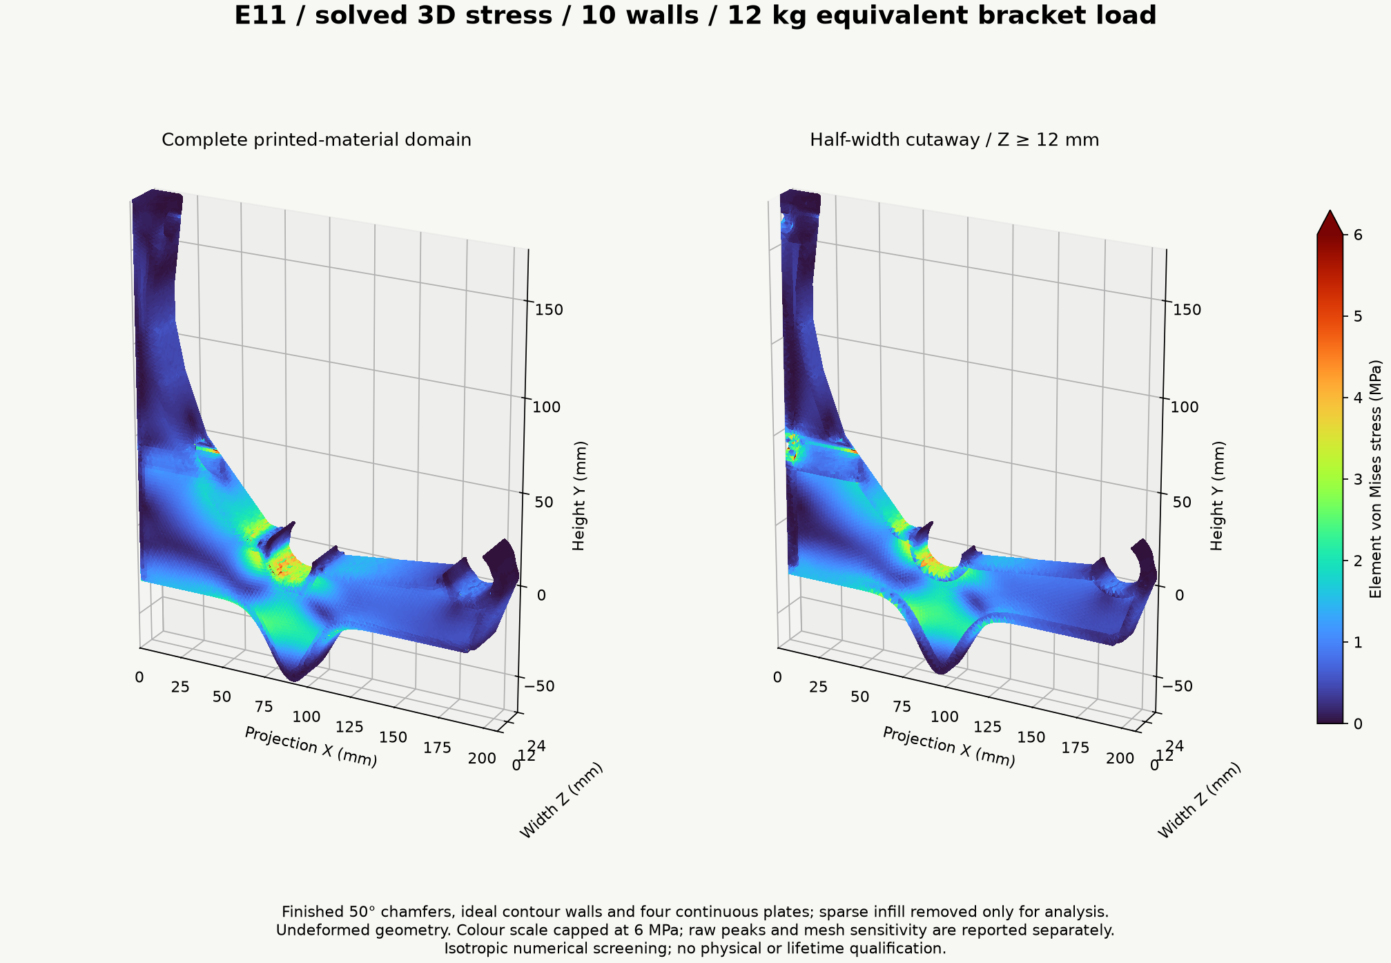
analysis/e11/fem-3d-10w.png
