thereprocase/spool-wall-rack/designs/closed-wall-d/progress-cutaway.png

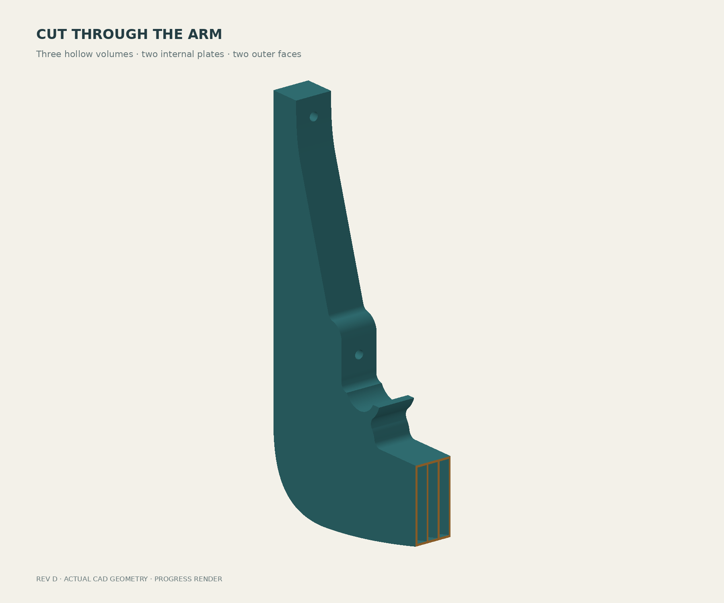
designs/closed-wall-d/progress-cutaway.png
