thereprocase/spool-wall-rack/designs/closed-wall-d/progress-exterior.png

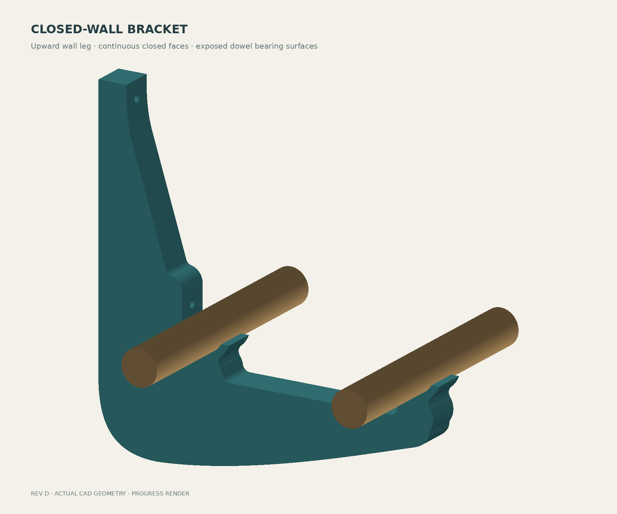
designs/closed-wall-d/progress-exterior.png
