thereprocase/spool-wall-rack/designs/closed-wall-d/progress-plates.png

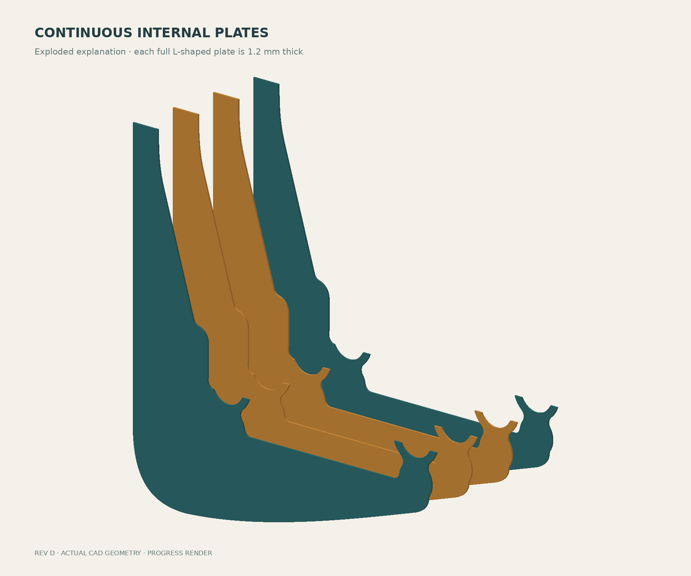
designs/closed-wall-d/progress-plates.png
