thereprocase/spool-wall-rack/designs/closed-wall-e5/progress-exterior.png

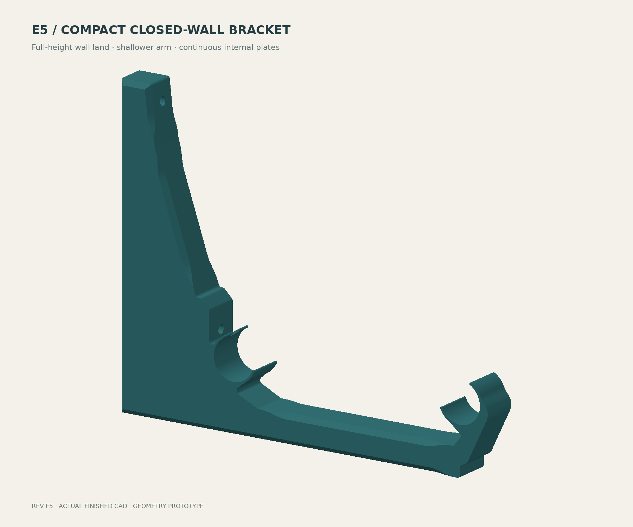
designs/closed-wall-e5/progress-exterior.png
