thereprocase/spool-wall-rack/designs/closed-wall-e5/retainer-engineering.png

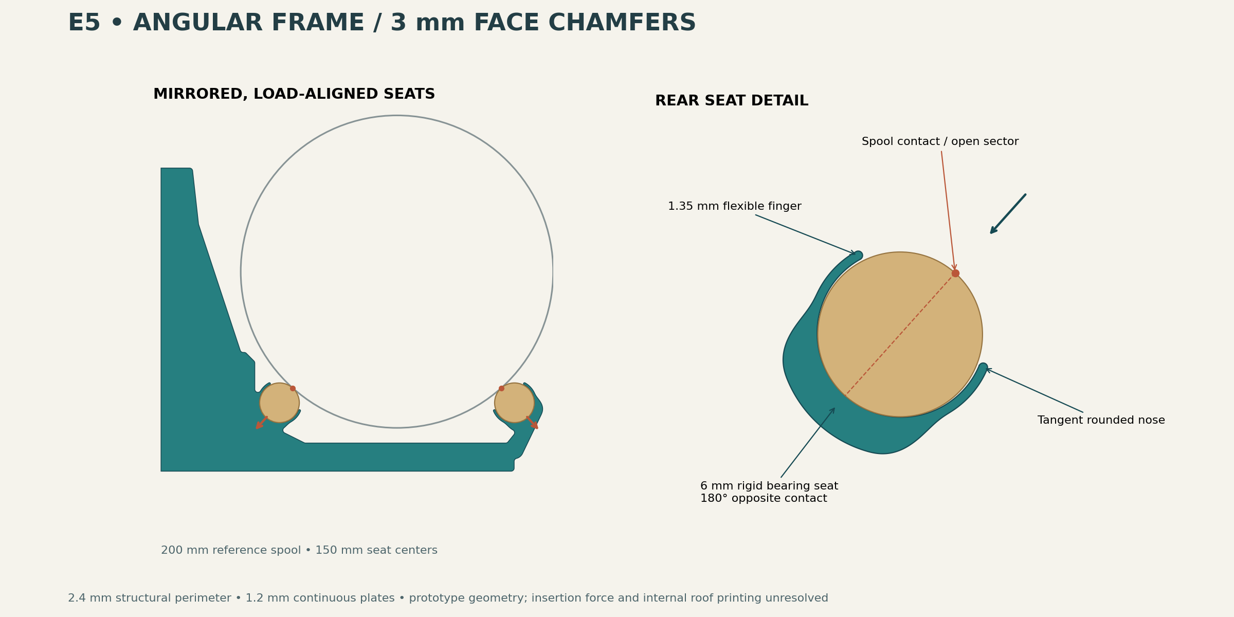
designs/closed-wall-e5/retainer-engineering.png
