thereprocase/spool-wall-rack/designs/closed-wall-e6/retainer-engineering.png

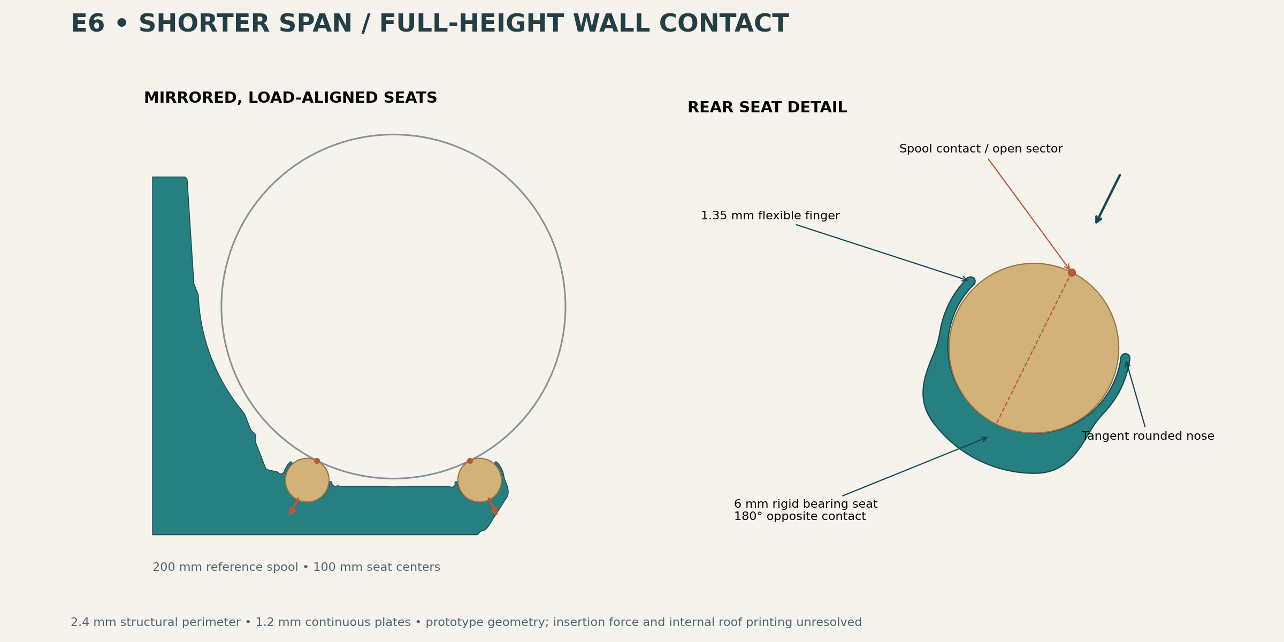
designs/closed-wall-e6/retainer-engineering.png
