thereprocase/spool-wall-rack/designs/closed-wall-e7/retainer-engineering.png

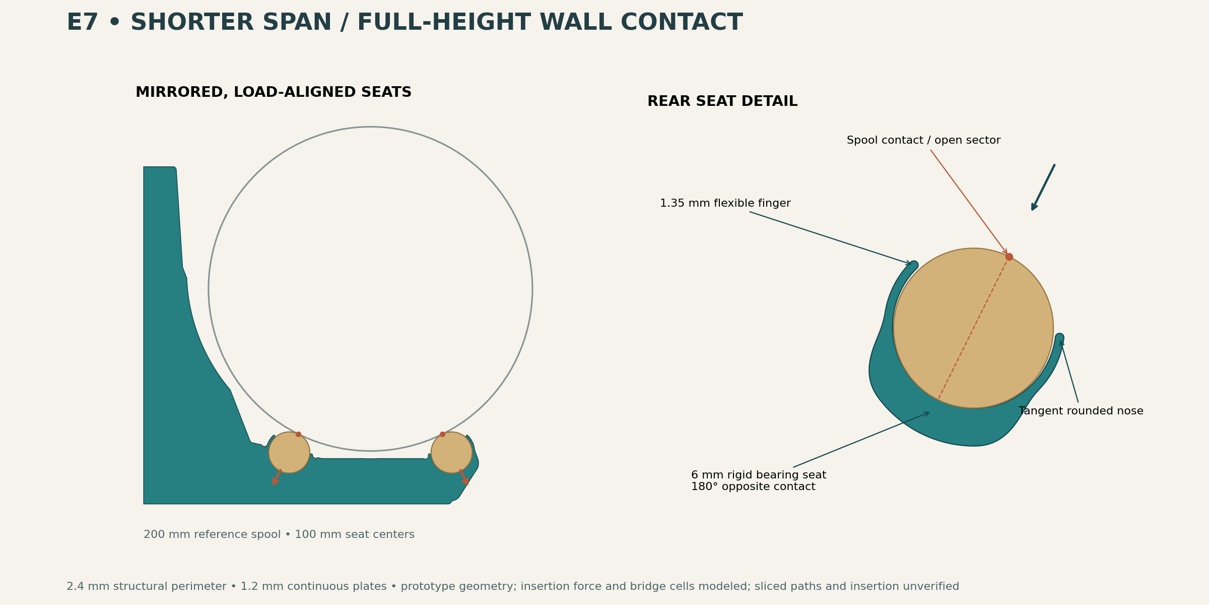
designs/closed-wall-e7/retainer-engineering.png
