thereprocase/spool-wall-rack/designs/closed-wall-e13/finish-inner-reverse.png

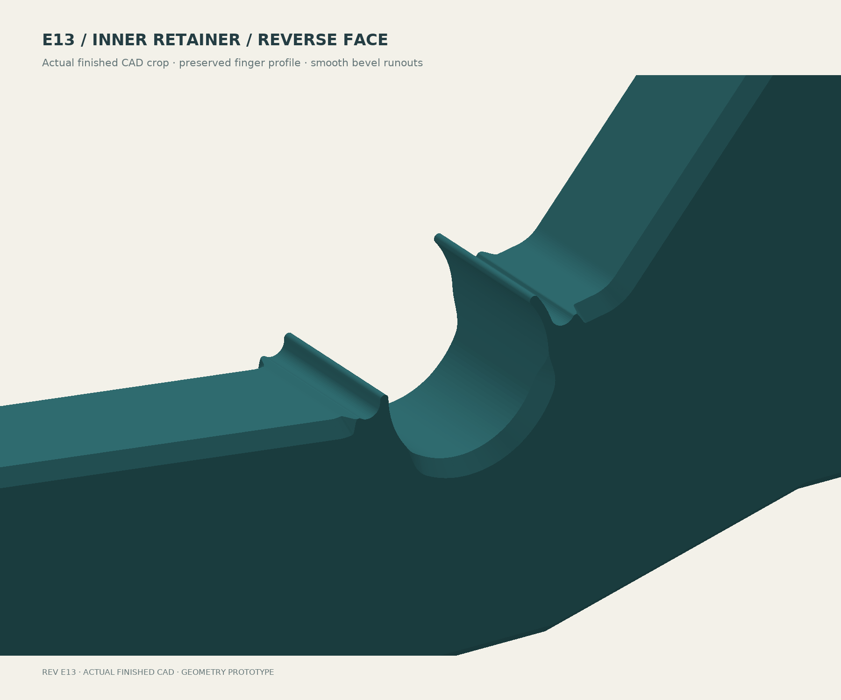
designs/closed-wall-e13/finish-inner-reverse.png
