thereprocase/spool-wall-rack/designs/closed-wall-e13/finish-outer-front.png

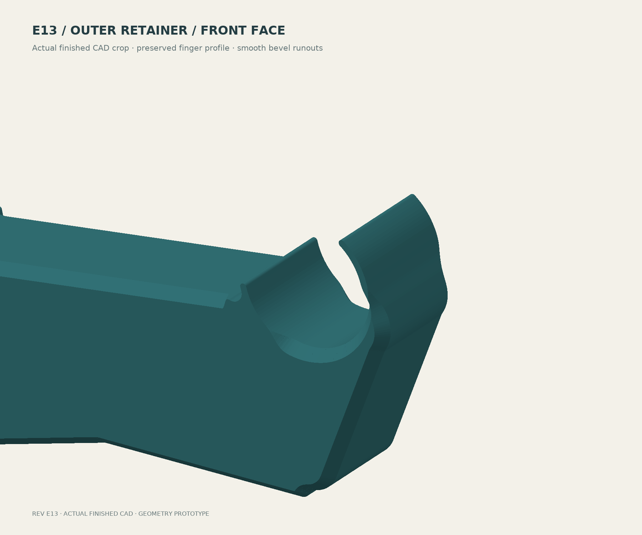
designs/closed-wall-e13/finish-outer-front.png
