thereprocase/spool-wall-rack/designs/closed-wall-e13/finish-outer-reverse.png

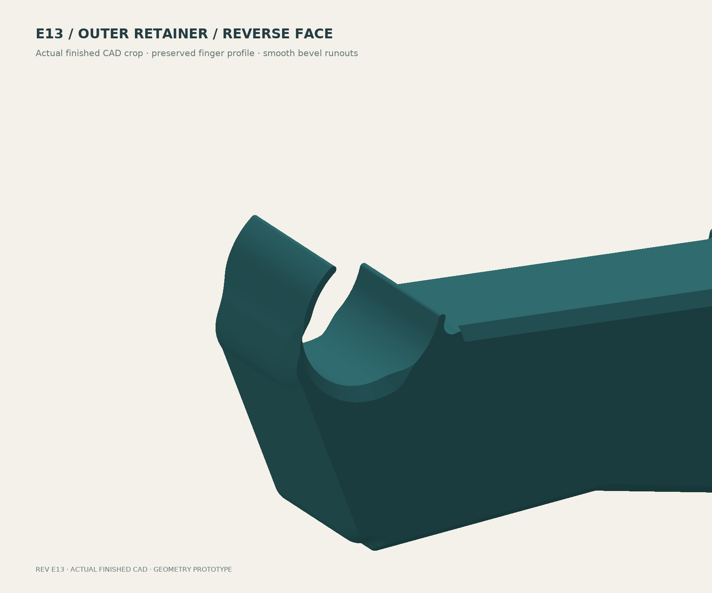
designs/closed-wall-e13/finish-outer-reverse.png
