thereprocase/spool-wall-rack/designs/closed-wall-e13/section-comparison.png

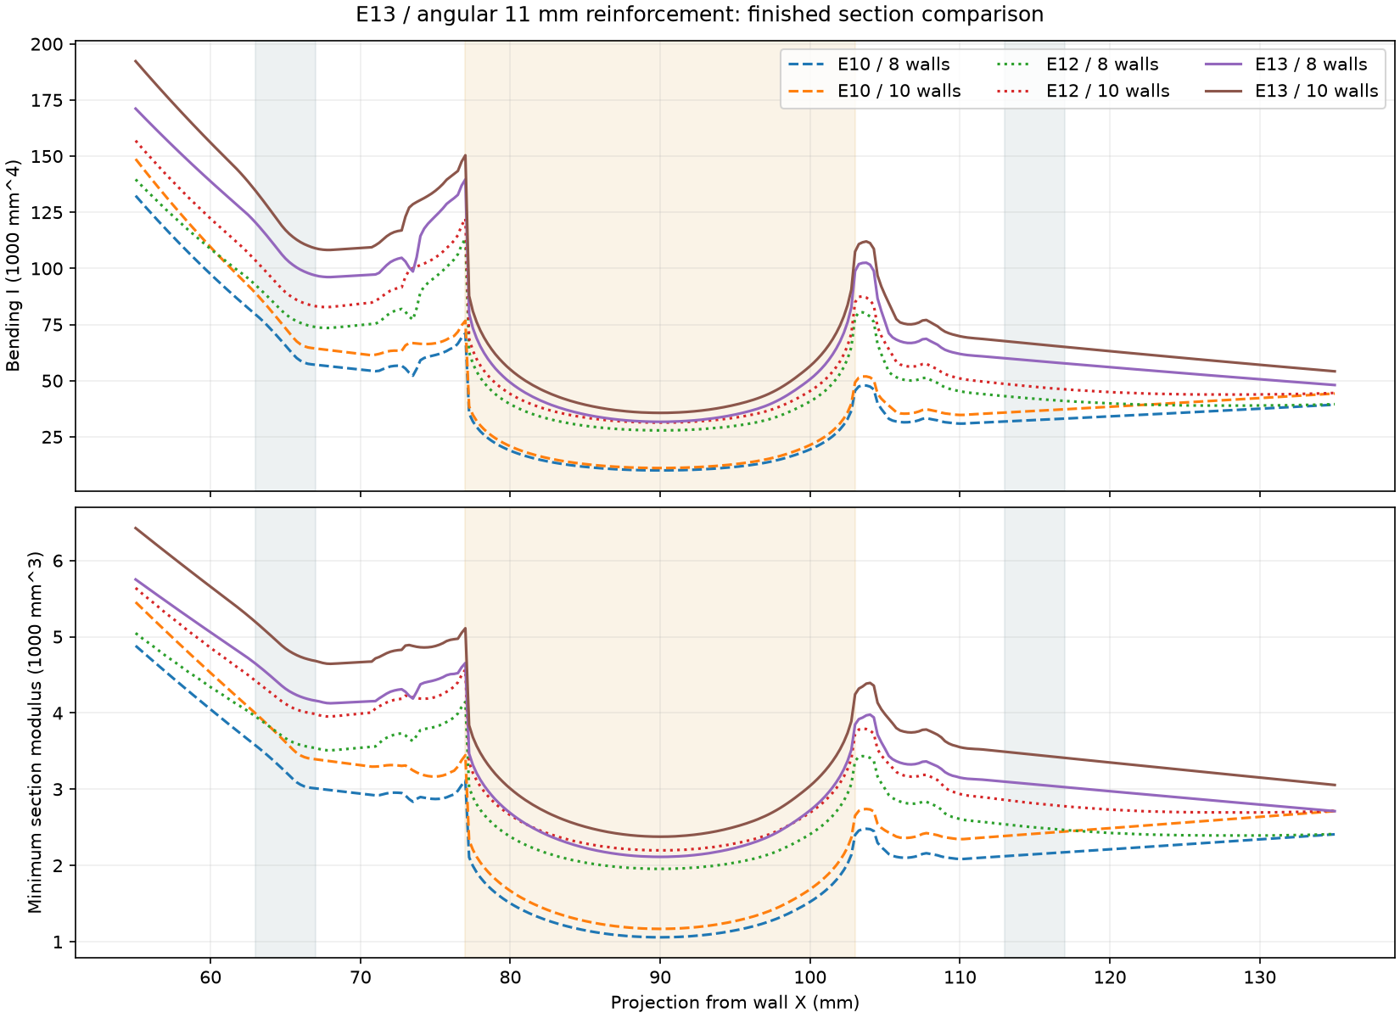
designs/closed-wall-e13/section-comparison.png
