thereprocase/spool-wall-rack/designs/rev-g2/ef-cut-v4/progress-exterior.png

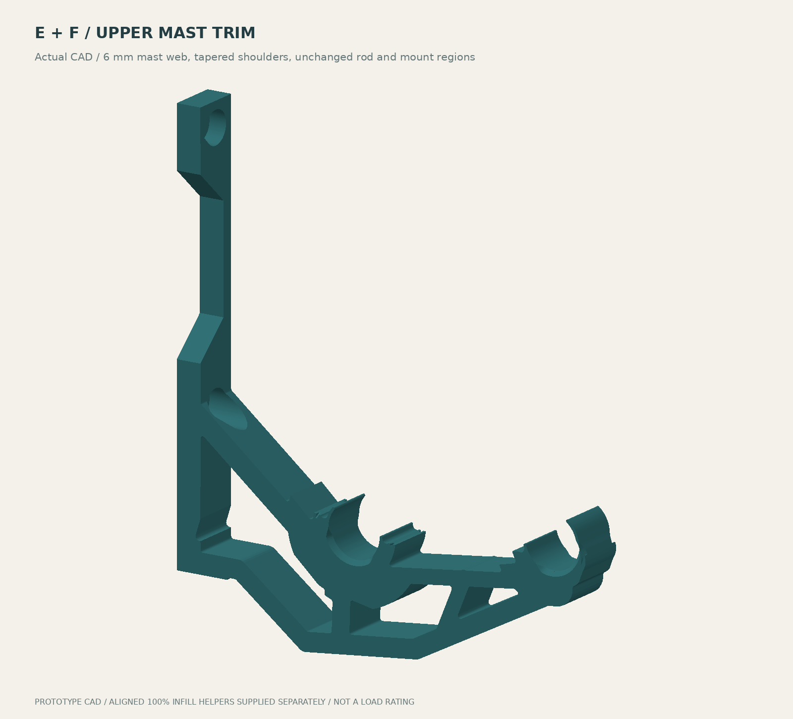
designs/rev-g2/ef-cut-v4/progress-exterior.png
