thereprocase/spool-wall-rack/designs/rev-g2/ef-hybrid-v1/direction.png

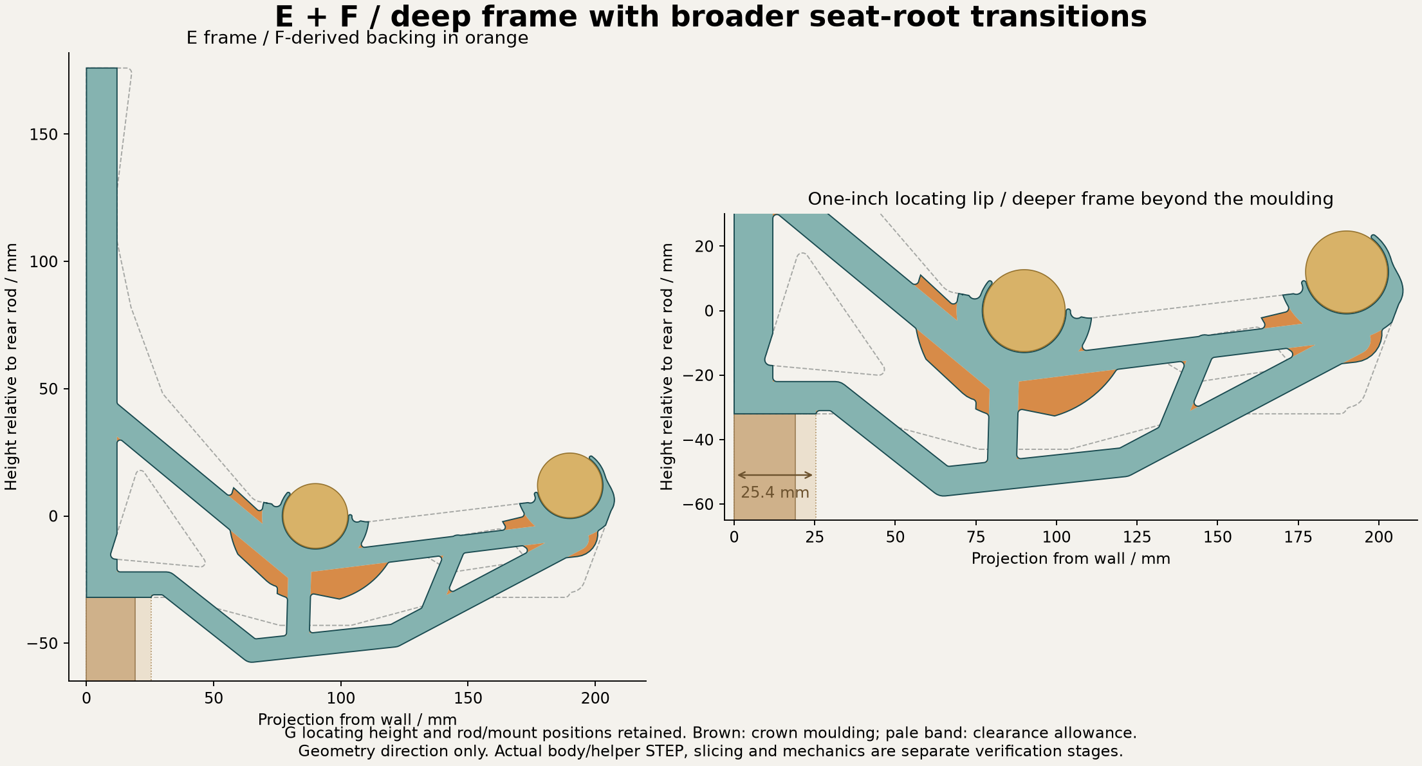
designs/rev-g2/ef-hybrid-v1/direction.png
