thereprocase/spool-wall-rack/designs/rev-g2/shape-seeds/A-shear-panels.png

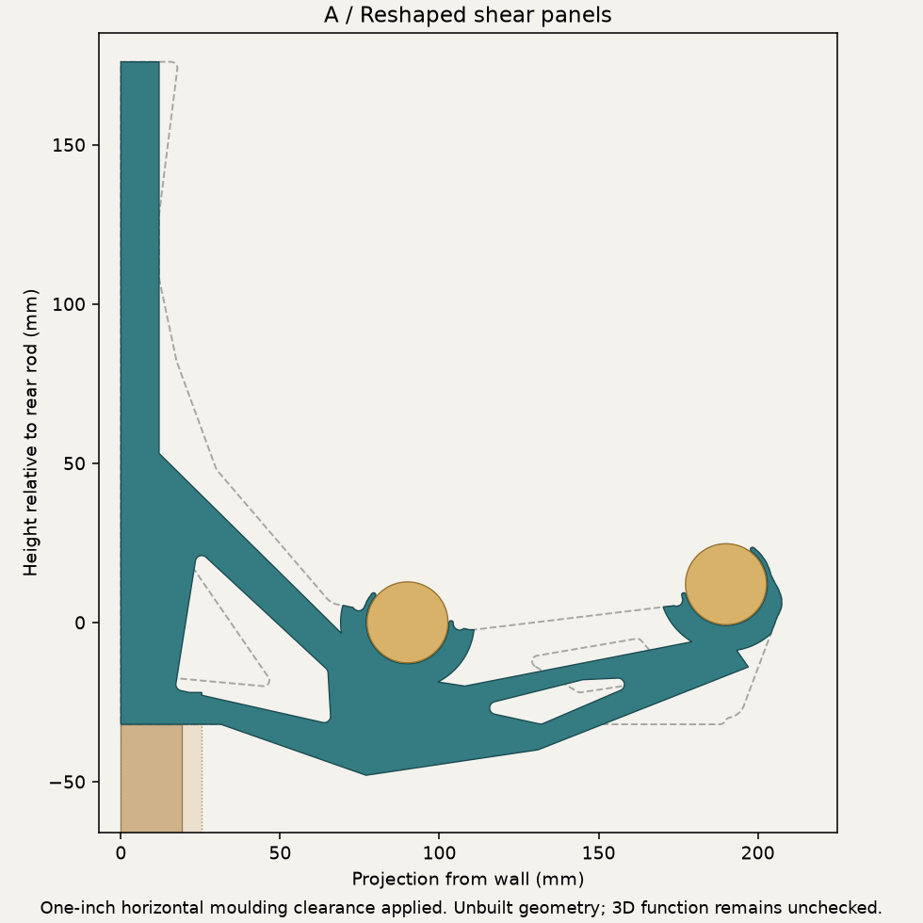
designs/rev-g2/shape-seeds/A-shear-panels.png
