thereprocase/spool-wall-rack/fit/rear-fit-coupon-with-helpers.step

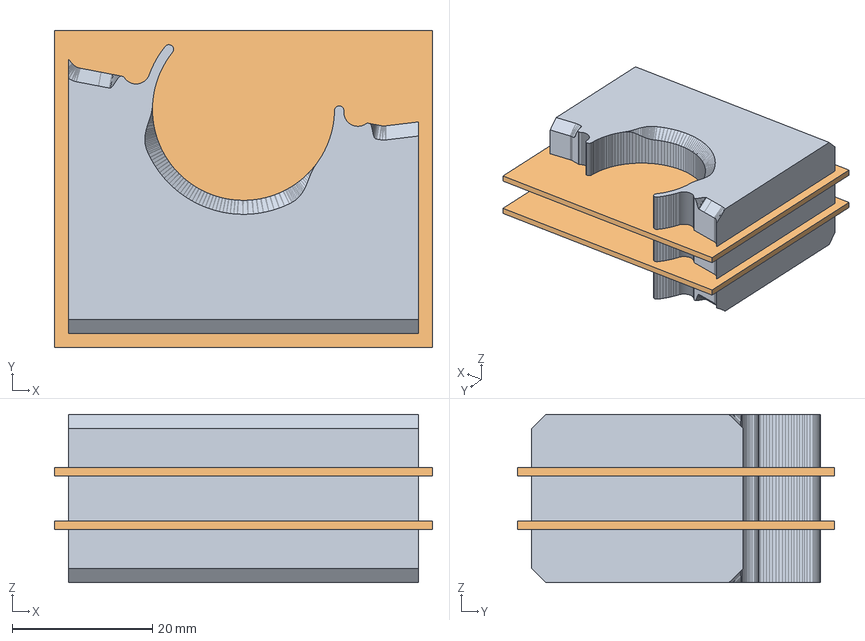
[picture p94: CAD file, 2026-09-10]
fit/rear-fit-coupon-with-helpers.step
54.0 x 45.2 x 24.0 mm
MAIN_BODY_SET_WALLS_AND_INFILL
MODIFIER_1_100_PERCENT_INFILL
MODIFIER_2_100_PERCENT_INFILL
