thereprocase/spool-wall-rack/designs/closed-wall-d/bracket.3mf

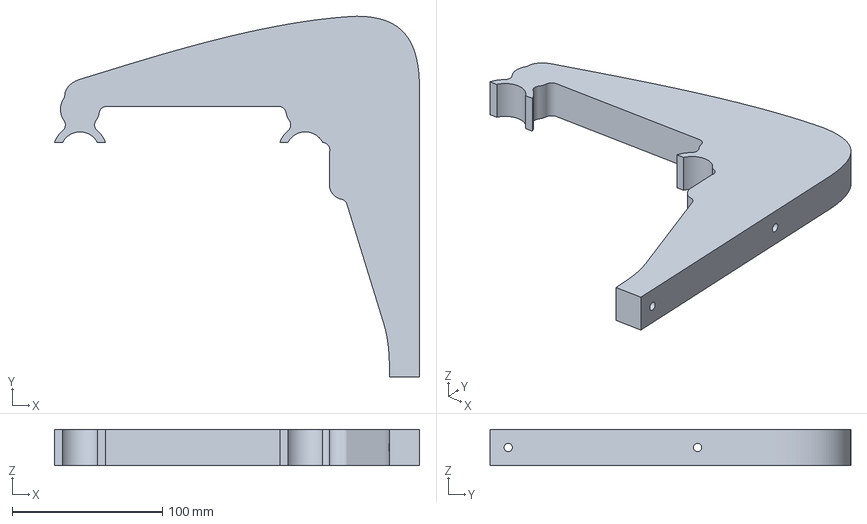
[picture p95: CAD file, 2026-09-10]
designs/closed-wall-d/bracket.3mf
243.0 x 240.0 x 24.0 mm
