thereprocase/spool-wall-rack/designs/closed-wall-e13/bracket-with-modifier-helpers.step

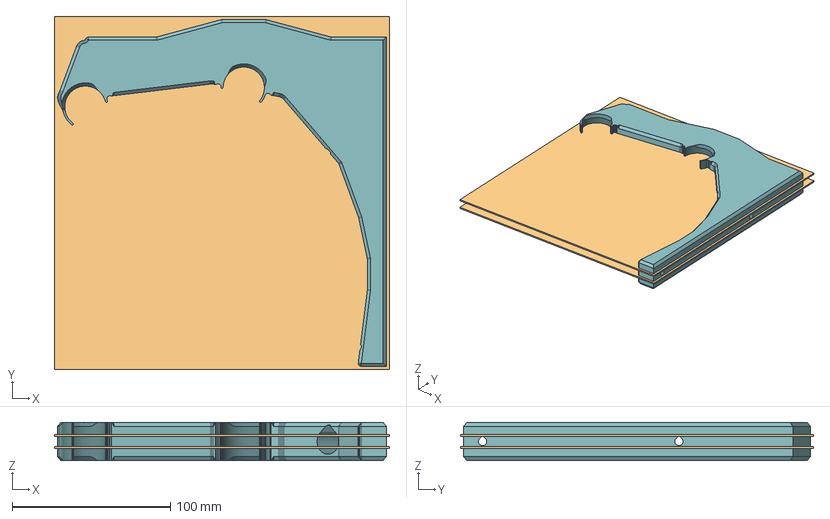
[picture p96: CAD file, 2026-09-10]
designs/closed-wall-e13/bracket-with-modifier-helpers.step
211.5 x 223.0 x 24.0 mm
MAIN_BODY_SET_WALLS_AND_INFILL
MODIFIER_1_100_PERCENT_INFILL_Z_7.6_TO_8.8_MM
MODIFIER_2_100_PERCENT_INFILL_Z_15.2_TO_16.4_MM
