thereprocase/spool-wall-rack/designs/closed-wall-e3/snap-coupon-8mm.stl

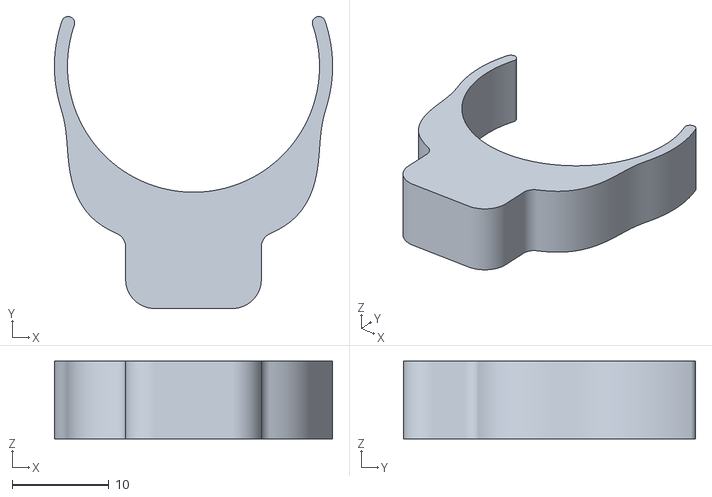
[picture p97: CAD file, 2026-09-10]
designs/closed-wall-e3/snap-coupon-8mm.stl
28.7 x 30.1 x 8.00
