thereprocase/spool-wall-rack/designs/closed-wall-e7/bridge-coupon.stl

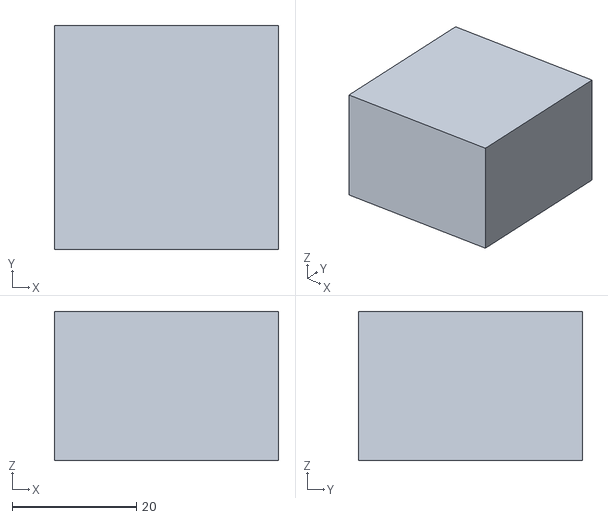
[picture p98: CAD file, 2026-09-10]
designs/closed-wall-e7/bridge-coupon.stl
36.0 x 36.0 x 24.0
