thereprocase/spool-wall-rack/designs/rev-g2/ef-hybrid-v1/body-only.step

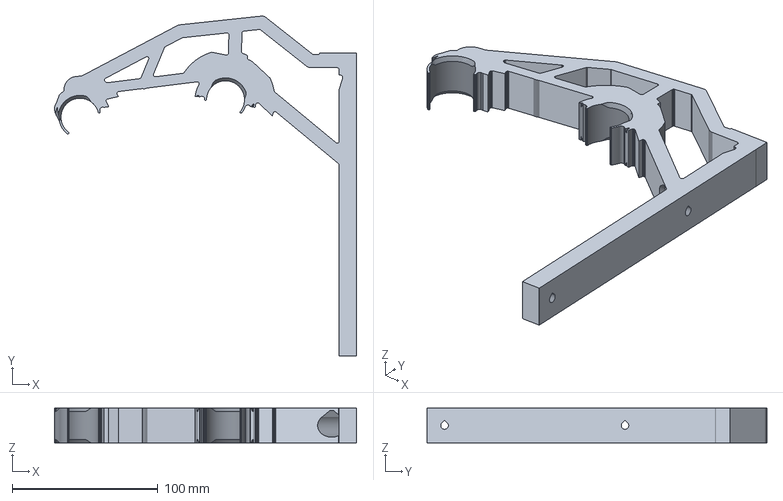
[picture p99: CAD file, 2026-09-11]
designs/rev-g2/ef-hybrid-v1/body-only.step
207.5 x 233.5 x 24.0 mm
