thereprocase/spool-wall-rack/designs/rev-g2/print-controls/g-asa-8w-1p6/dense-chords-and-seats.step

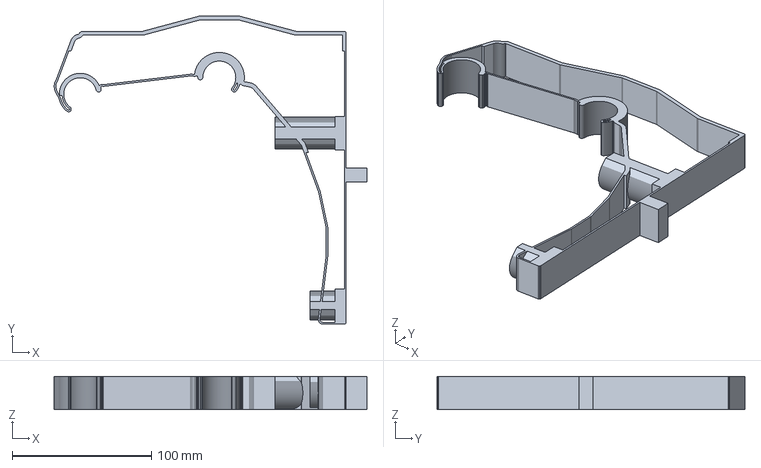
[picture p100: CAD file, 2026-09-11]
designs/rev-g2/print-controls/g-asa-8w-1p6/dense-chords-and-seats.step
224.7 x 221.4 x 24.0 mm
