thereprocase/spool-wall-rack/fit/front-fit-coupon-with-helpers.step

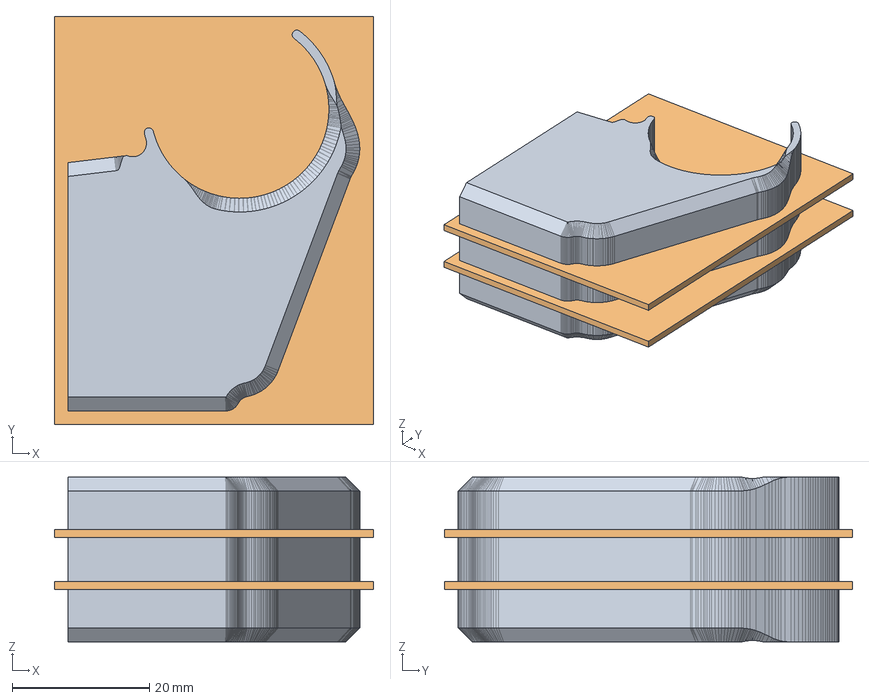
[picture p101: CAD file, 2026-09-10]
fit/front-fit-coupon-with-helpers.step
46.5 x 59.5 x 24.0 mm
MAIN_BODY_SET_WALLS_AND_INFILL
MODIFIER_1_100_PERCENT_INFILL
MODIFIER_2_100_PERCENT_INFILL
