thereprocase/spool-wall-rack/designs/closed-wall-d/arm-section.stl

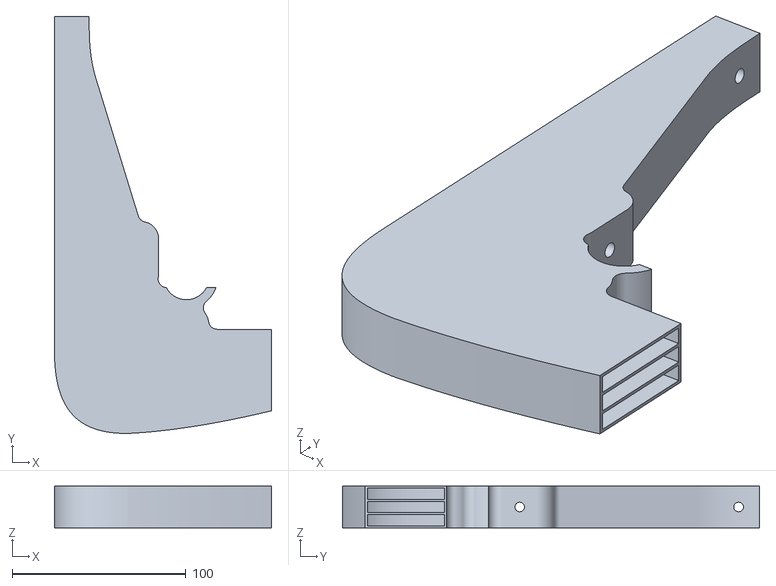
[picture p102: CAD file, 2026-09-10]
designs/closed-wall-d/arm-section.stl
125.0 x 240.0 x 24.0
