thereprocase/spool-wall-rack/designs/closed-wall-e7/cutaway.stl

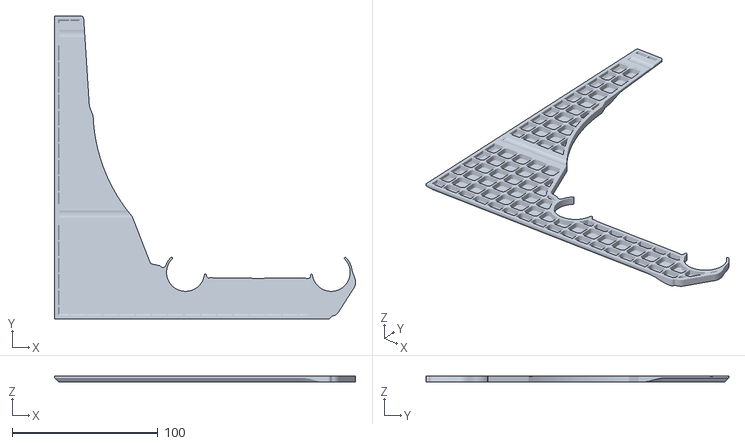
[picture p103: CAD file, 2026-09-10]
designs/closed-wall-e7/cutaway.stl
206.7 x 208.0 x 4.40
