thereprocase/spool-wall-rack/designs/rev-g2/ef-hybrid-v1/dense-chords-and-seats.step

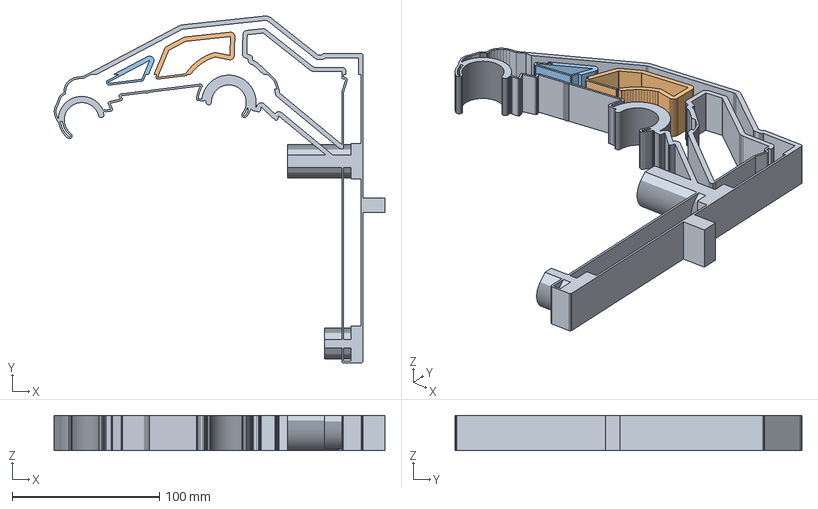
[picture p104: CAD file, 2026-09-11]
designs/rev-g2/ef-hybrid-v1/dense-chords-and-seats.step
224.7 x 235.9 x 24.0 mm
