thereprocase/spool-wall-rack/designs/rev-g2/ef-reinvest-v2/local-transition-backing.step

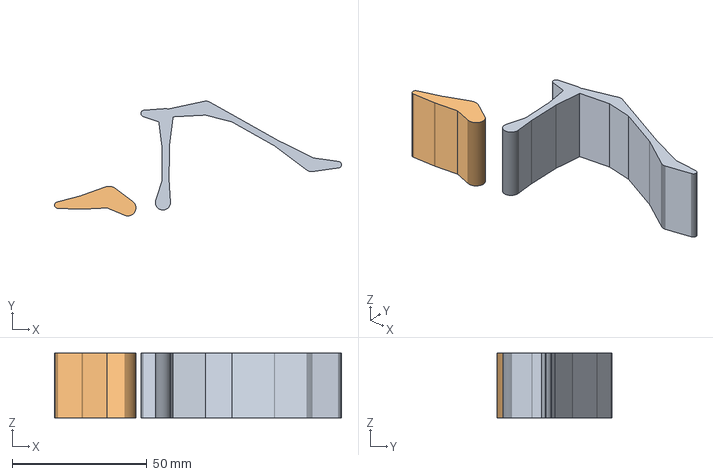
[picture p105: CAD file, 2026-09-11]
designs/rev-g2/ef-reinvest-v2/local-transition-backing.step
106.4 x 42.6 x 24.0 mm
