thereprocase/spool-wall-rack/designs/rev-g2/print-controls/g-asa-4w-1p6/rib-plane-upper.step

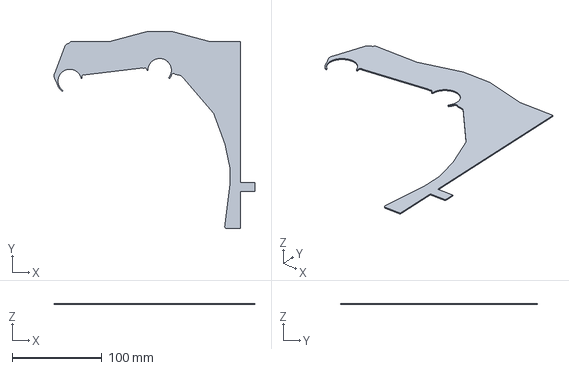
[picture p106: CAD file, 2026-09-11]
designs/rev-g2/print-controls/g-asa-4w-1p6/rib-plane-upper.step
223.5 x 219.0 x 1.00 mm
