thereprocase/spool-wall-rack/fit/front-fit-coupon.step

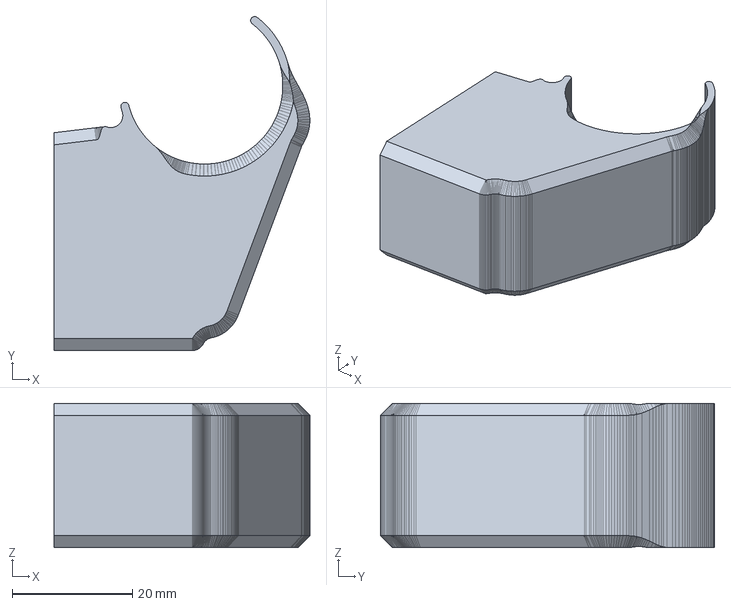
[picture p107: CAD file, 2026-09-10]
fit/front-fit-coupon.step
42.5 x 55.5 x 24.0 mm
