thereprocase/spool-wall-rack/designs/closed-wall-d/bridge-coupon.stl

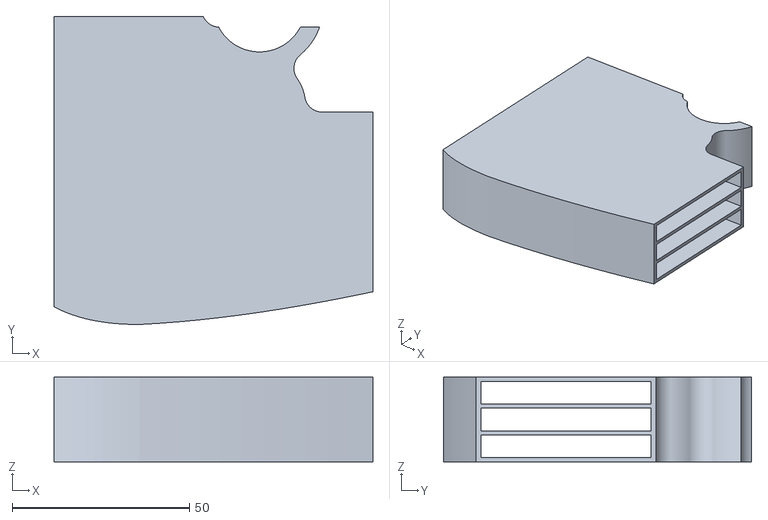
[picture p108: CAD file, 2026-09-10]
designs/closed-wall-d/bridge-coupon.stl
90.0 x 87.0 x 24.0
