thereprocase/spool-wall-rack/designs/closed-wall-e13/body-mounted.stl

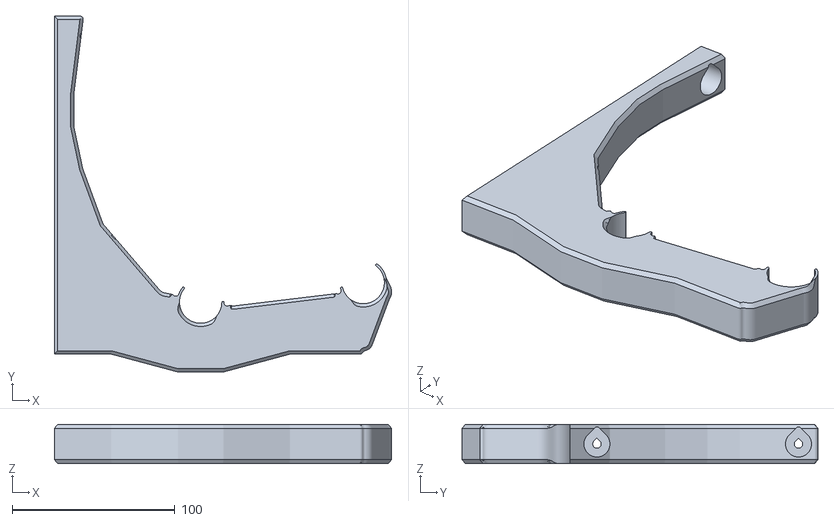
[picture p109: CAD file, 2026-09-10]
designs/closed-wall-e13/body-mounted.stl
207.5 x 219.0 x 24.0
