thereprocase/spool-wall-rack/designs/closed-wall-e7/mounted.stl

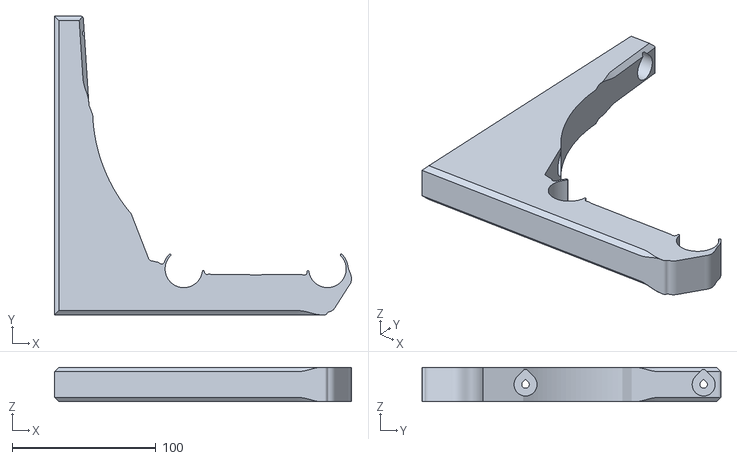
[picture p110: CAD file, 2026-09-10]
designs/closed-wall-e7/mounted.stl
206.7 x 208.0 x 24.0
