thereprocase/spool-wall-rack/designs/rev-g2/ef-cut-v4/central-rib-plane.step

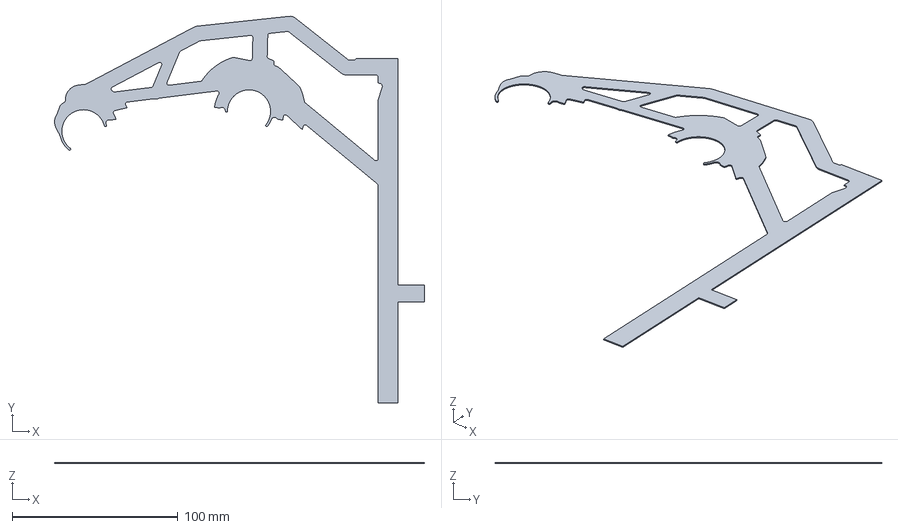
[picture p111: CAD file, 2026-09-11]
designs/rev-g2/ef-cut-v4/central-rib-plane.step
223.5 x 233.5 x 0.6 mm
