thereprocase/spool-wall-rack/fit/rear-fit-coupon.step

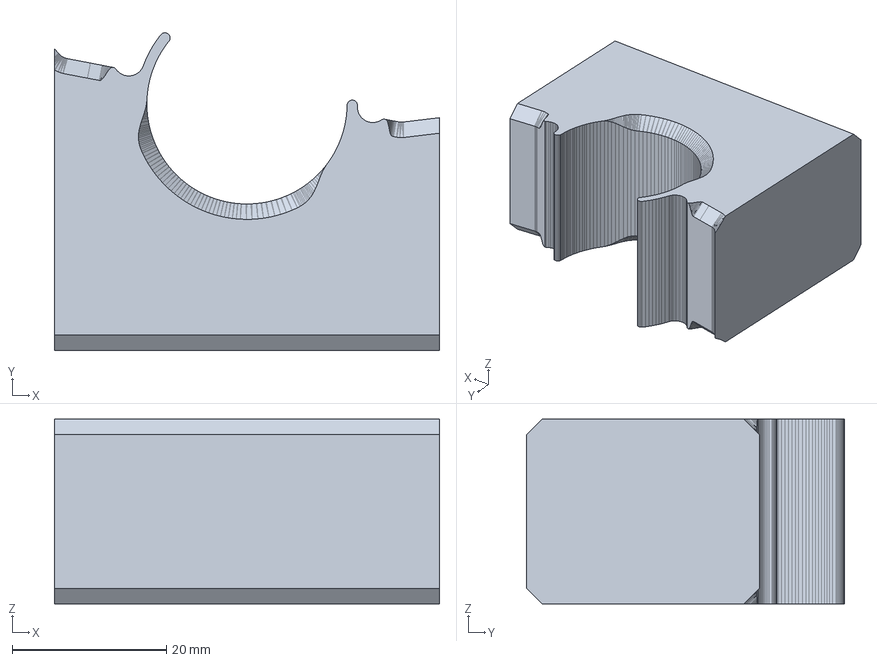
[picture p112: CAD file, 2026-09-10]
fit/rear-fit-coupon.step
50.0 x 41.2 x 24.0 mm
