thereprocase/spool-wall-rack/designs/rev-g2/ef-cut-v4/dense-chords-and-seats.step

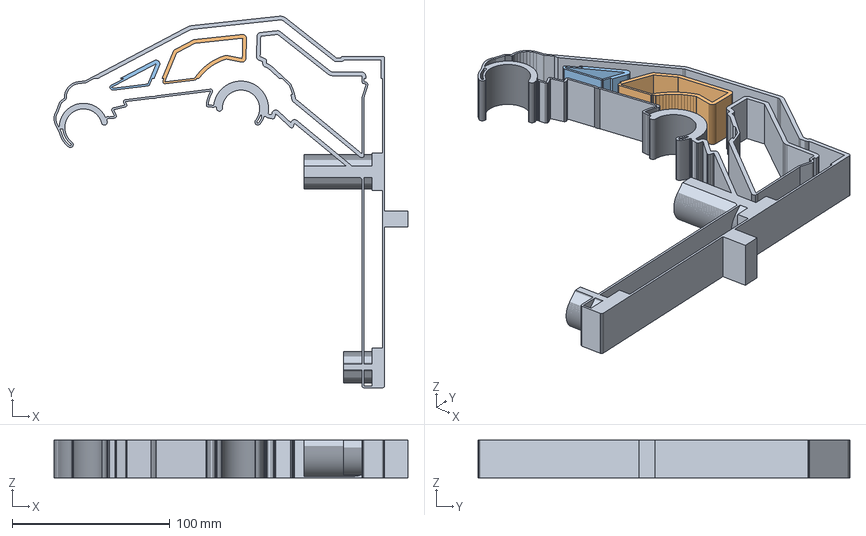
[picture p113: CAD file, 2026-09-11]
designs/rev-g2/ef-cut-v4/dense-chords-and-seats.step
224.7 x 235.9 x 24.0 mm
