thereprocase/spool-wall-rack/analysis/rev-g2/evolution-results/batch-02/scores.csv

id | generation | status | bottom_band | diagonal_band | seat_band | front_seat_band | lower_tunnel_collar_mm | upper_tunnel_collar_mm | volume_ratio | movement_indicator_mm | raw_2d_peak_MPa | inner_seat_ratio | score
23f9a4e917d5 | 0 | PASS_REDUCED_CONTACT | 1.45 | 1.8 | 5.0 | 2.0 | 3.5 | 2.5 | 0.9941807125242303 | 4.416765988503179 | 17.806267806267805 | 1.0101054427570928 | 1.3638192913283012
9cb28e5dabb4 | 0 | PASS_REDUCED_CONTACT | 1.75 | 1.8 | 5.0 | 2.0 | 3.5 | 2.5 | 1.0068318654696402 | 4.289565957329995 | 13.231957024806489 | 0.9956213393731875 | 1.0697182102615086
14648bf1e012 | 0 | PASS_REDUCED_CONTACT | 1.6 | 1.65 | 5.0 | 2.0 | 3.5 | 2.5 | 0.998679633148421 | 4.350726550227481 | 36.97866974158532 | 1.000033621503312 | 7.534021278803243
4edca4daafbb | 0 | PASS_REDUCED_CONTACT | 1.6 | 1.95 | 5.0 | 2.0 | 3.5 | 2.5 | 1.0058798487264 | 4.282101826158491 | 13.205016249649194 | 0.9999115492943113 | 1.0655659289678665
9be1dd4d87d3 | 0 | PASS_REDUCED_CONTACT | 1.6 | 1.8 | 4.5 | 2.0 | 3.5 | 2.5 | 0.9925506017515893 | 4.370953091956111 | 13.229688294071181 | 1.058971758444799 | 1.102710585663582
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
